Electrics-Eagles/Electric-Eagles/Documents/Safety/Drones and Battery  safety.pdf

Drones and Battery safety.

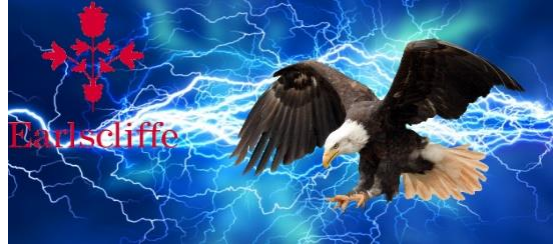
[picture p3: figure]

### 1 When somebody runs drone , everybody else wear

glasses ! And don`t go to drone near than 2 meters.

### 2 When command “Take off” is said everybody goes

away from drone to safe distance*.

### 3 When drone touches down nobody go near to

drone while command “Copter Disarmed” is said.

### 4 If you want change something in drone firstly

disconnect a battery.

### 5 When you flight with copter , do all movements

with sticks slowly.

### 6 Don`t leave battery in drone. Put it in safety

box**

### 7 Charge battery only using calibrated checked

charger . (During charging process don`t leave a room where it happened.

### 8 Think before do !

*- A metal isolated box .
** - Like IMAX B6 and others
