Electrics-Eagles/Electric-Eagles/Modules/EasyFly/Android APP/AndroidUSBCamera-master/gifs/download.png

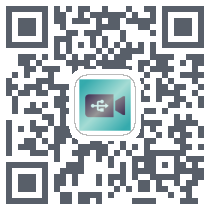
Modules/EasyFly/Android APP/AndroidUSBCamera-master/gifs/download.png
