Electrics-Eagles/Electric-Eagles/Tools Code/Died Tools/CopterChecktool/error.png

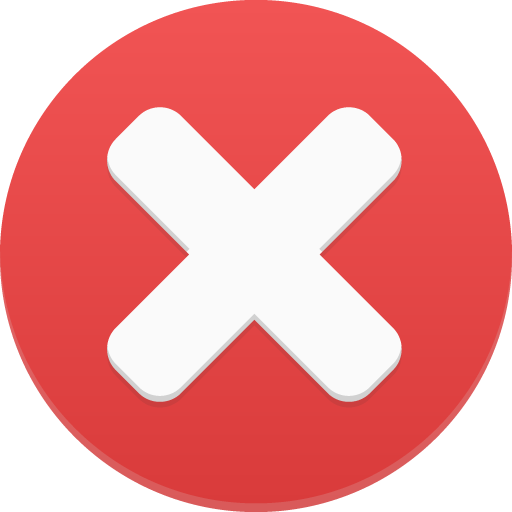
Tools Code/Died Tools/CopterChecktool/error.png
