Electrics-Eagles/Electric-Eagles/Tools Code/Died Tools/CopterChecktool/ok.png

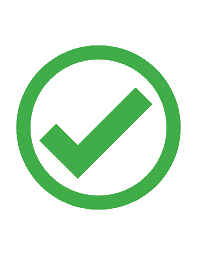
Tools Code/Died Tools/CopterChecktool/ok.png
