Electrics-Eagles/Electric-Eagles/Studio/Bugs/Build System. · Issue #3 · alex5250_ElectricsEaglesStudio.pdf

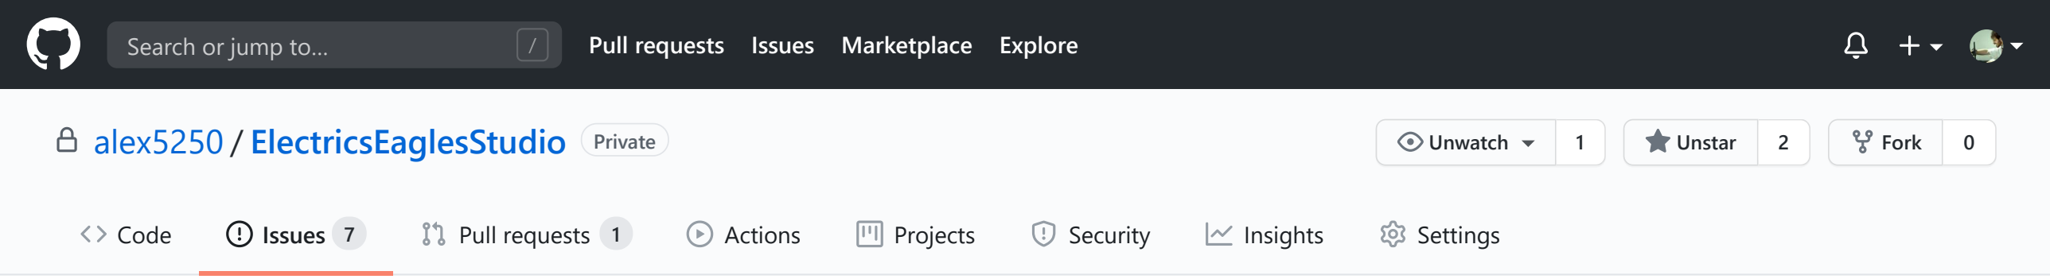
[picture p36: figure]
Code; Issues; Pull requests; Actions; Projects; Security; Insights; Settings; Search or jump to…; Pull requests Issues Marketplace Explore; Unwatch; Unstar; Fork

alex5250 (https://github.com/alex5250) / ElectricsEaglesStudio (https://github.com/alex5250/ElectricsEaglesStudio) Private

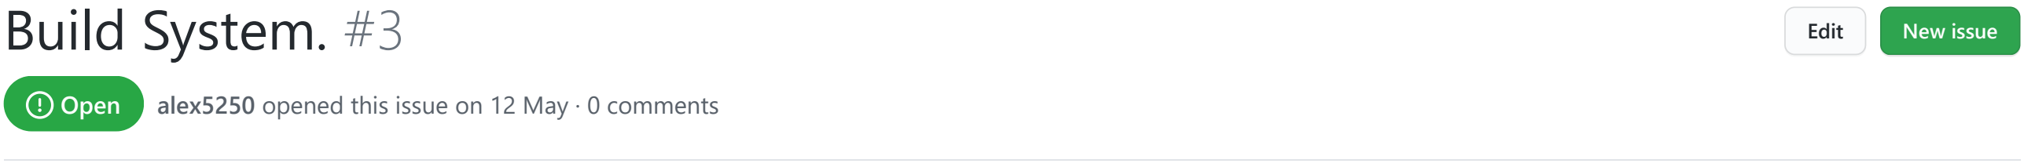
[picture p37: figure]
Build System. #3; Edit; New issue

Open alex5250 (https://github.com/alex5250) opened this issue on 12 May · 0 comments

No one—assign yourself

None yet

No milestone

Successfully merging a pull request may close this issue.
None yet

### 1 participant

Lock conversation

Pin issue

Transfer issue

Delete issue

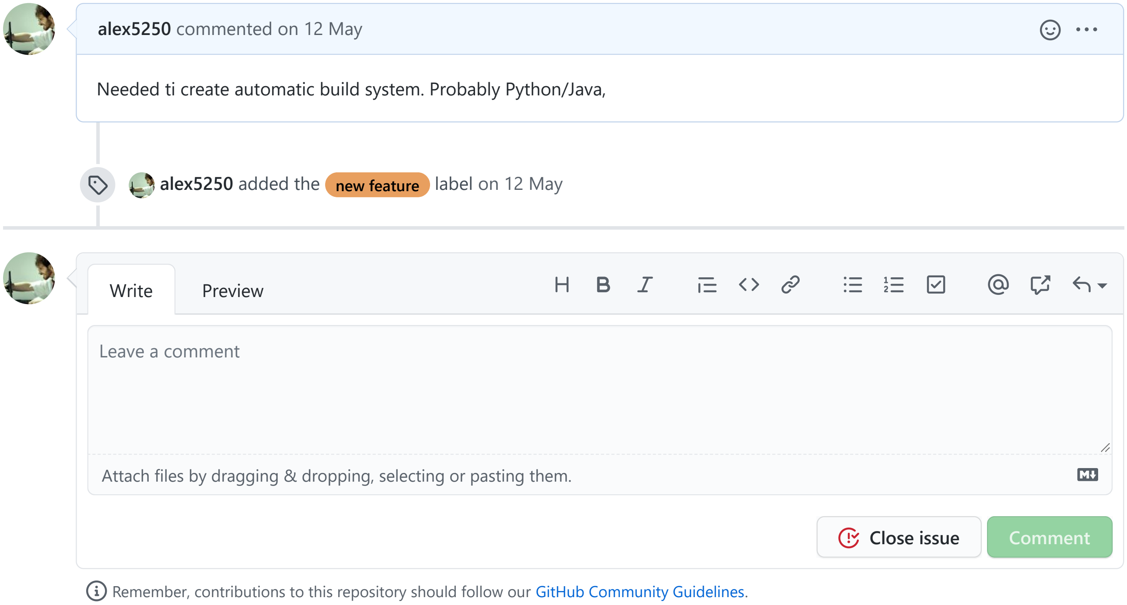
[picture p38: figure]
alex5250 commented on 12 May; alex5250 added the; new feature; label on 12 May; Leave a comment; Choose Files No file chosen; Close issue; Comment; Write; Preview

Needed ti create automatic build system. Probably Python/Java,

Remember, contributions to this repository should follow our GitHub Community Guidelines. (https://docs.github.com/articles/github-community-guidelines)

Attach files by dragging & dropping, selecting or pasting them.

Assignees

Labels

new feature (https://github.com/alex5250/ElectricsEaglesStudio/labels/new%20feature)

Projects

Milestone

Linked pull requests

You’re receiving notifications because you’re watching this repository.

Notifications | Customize

Unsubscribe

© 2020 GitHub, Inc. | Terms (https://github.com/site/terms) | Privacy (https://github.com/site/privacy) | Security (https://github.com/security) | Status (https://githubstatus.com/) | Help (https://docs.github.com/) | Contact GitHub (https://github.com/contact) | Pricing (https://github.com/pricing) | API (https://docs.github.com/) | Training (https://services.github.com/) | Blog (https://github.blog/) | About (https://github.com/about)
