Electrics-Eagles/Electric-Eagles/Studio/Electrics Eagles Setup Studio/src/main/resources/code.jpg

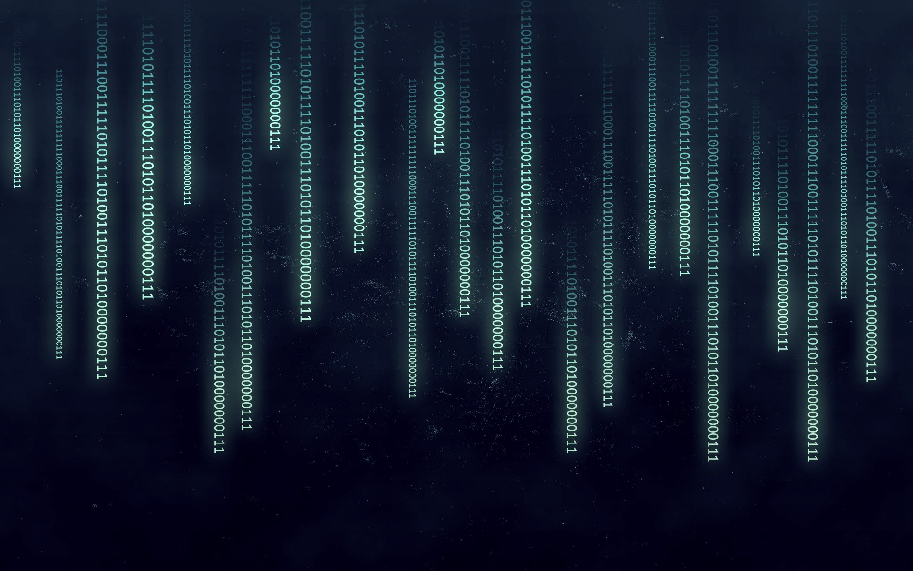
Studio/Electrics Eagles Setup Studio/src/main/resources/code.jpg
