Electrics-Eagles/Electric-Eagles/Studio/Electrics Eagles Setup Studio/src/main/resources/flash.png

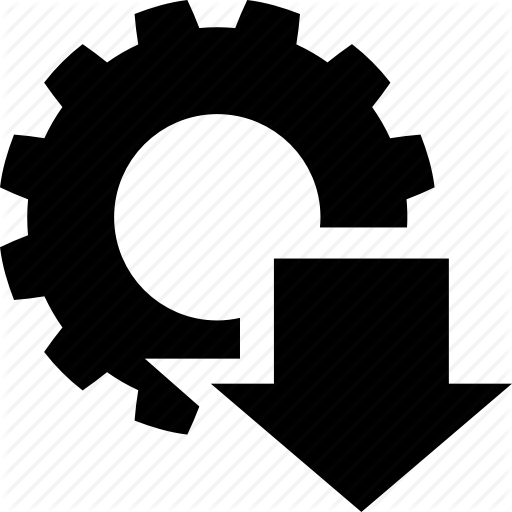
Studio/Electrics Eagles Setup Studio/src/main/resources/flash.png
