Electrics-Eagles/Electric-Eagles/Studio/Electrics Eagles Setup Studio/src/main/resources/Imanges/output_pd9a2z.gif

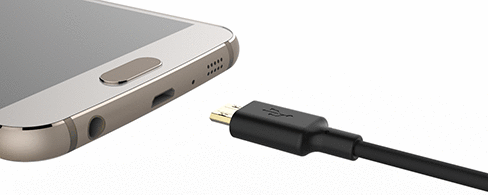
Studio/Electrics Eagles Setup Studio/src/main/resources/Imanges/output_pd9a2z.gif
