Electrics-Eagles/Electric-Eagles/Studio/Electrics Eagles Setup Studio/src/main/resources/Imanges/s7_usb_250px.gif

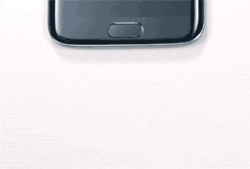
Studio/Electrics Eagles Setup Studio/src/main/resources/Imanges/s7_usb_250px.gif
