Electrics-Eagles/Electric-Eagles/Studio/Electrics Eagles Setup Studio/src/main/resources/pid.png

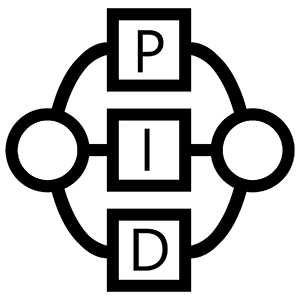
Studio/Electrics Eagles Setup Studio/src/main/resources/pid.png
