Electrics-Eagles/Electric-Eagles/Studio/Electrics Eagles Setup Studio/src/main/resources/usb-1831628-1554572.png

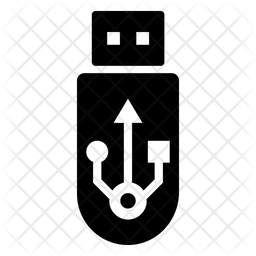
Studio/Electrics Eagles Setup Studio/src/main/resources/usb-1831628-1554572.png
