Electrics-Eagles/Electric-Eagles/Studio/Electrics Eagles Setup Studio/src/main/resources/VX2OTxL2oC.png

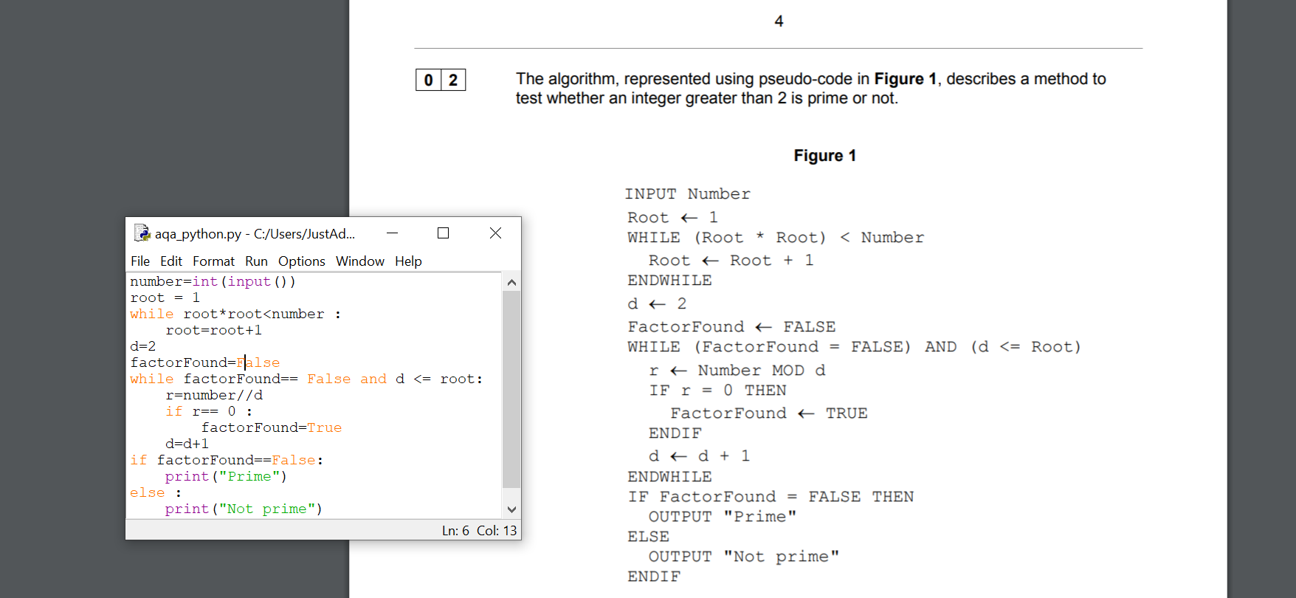
Studio/Electrics Eagles Setup Studio/src/main/resources/VX2OTxL2oC.png
