Electrics-Eagles/Electric-Eagles/Studio/Electrics Eagles Setup Studio/src/main/resources/x-512.png

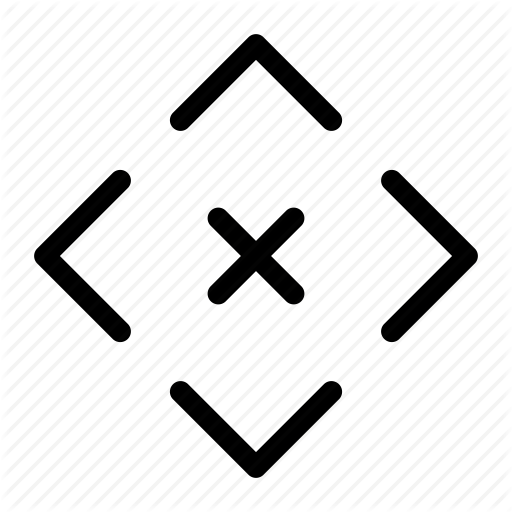
Studio/Electrics Eagles Setup Studio/src/main/resources/x-512.png
