Electrics-Eagles/Electric-Eagles/Studio/Bugs/PID Calibrate Button is not Working · Issue #12 · alex5250_ElectricsEaglesStudio.pdf

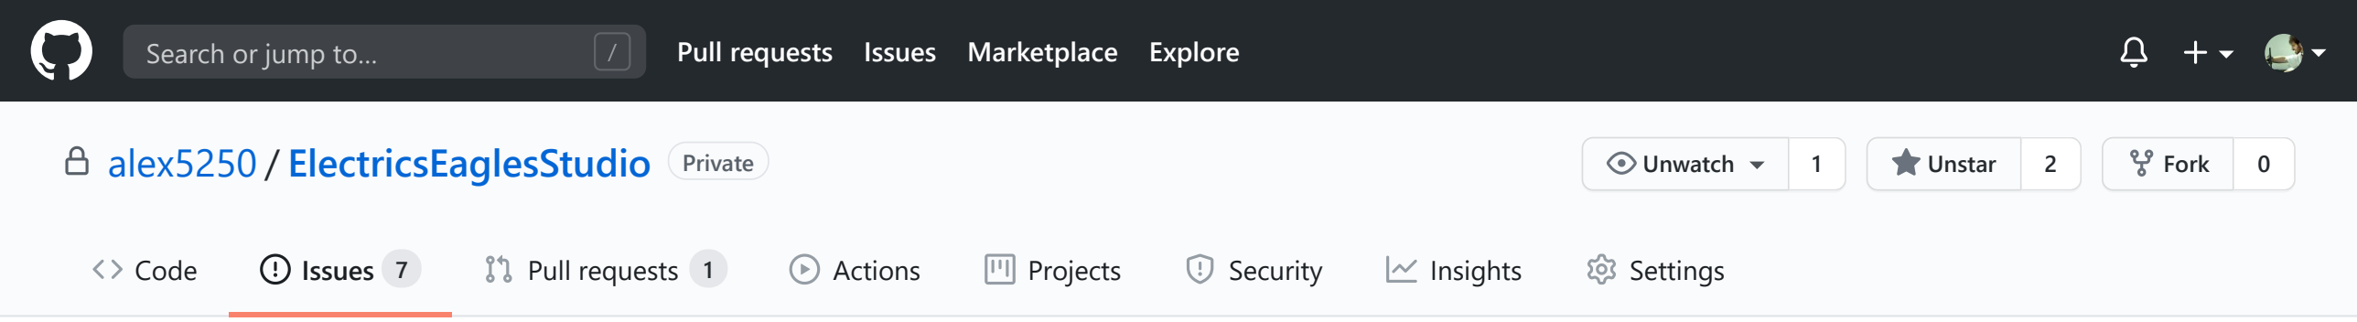
[picture p50: figure]
Unwatch; Unstar; Fork

alex5250 (https://github.com/alex5250) / ElectricsEaglesStudio (https://github.com/alex5250/ElectricsEaglesStudio) Private

Code (https://github.com/alex5250/ElectricsEaglesStudio) | Issues | 7 (https://github.com/alex5250/ElectricsEaglesStudio/issues) | Pull requests | 1 (https://github.com/alex5250/ElectricsEaglesStudio/pulls) | Actions (https://github.com/alex5250/ElectricsEaglesStudio/actions) | Projects (https://github.com/alex5250/ElectricsEaglesStudio/projects) | Security (https://github.com/alex5250/ElectricsEaglesStudio/security) | Insights (https://github.com/alex5250/ElectricsEaglesStudio/network/dependencies) | Settings (https://github.com/alex5250/ElectricsEaglesStudio/settings)

# PID Calibrate Button is not Working #12

## Open alex5250 (https://github.com/alex5250) opened this issue on 15 May · 0 comments

No one—assign yourself

None yet

No milestone

Successfully merging a pull request may close this issue.
None yet

### 1 participant

Lock conversation

Pin issue

Transfer issue

Delete issue

Search or jump to… | Pull requests (https://github.com/pulls) Issues (https://github.com/issues) Marketplace (https://github.com/marketplace) Explore (https://github.com/explore)
Edit | New issue (https://github.com/alex5250/ElectricsEaglesStudio/issues/new/choose)

## alex5250 (https://github.com/alex5250) commented on 15 May •

## 1. I opened a studio 2. Clicked an Open PID/Setup settings 3.Enter values

3. Press save values.

## 4. Pressed flash drone

5. I had an error.

## log.txt (https://github.com/alex5250/ElectricsEaglesStudio/files/4636048/log.txt)

system_info.txt (https://github.com/alex5250/ElectricsEaglesStudio/files/4636028/system_info.txt)

I got bug.

[INFO] Fri May 15 17:56:49 BST 2020 Found boards[Ljava.lang.String;@742f7e36 EXPORT TO : log.txt
[INFO] Fri May 15 17:56:52 BST 2020 Python is found EXPORT TO : log.txt
[ERROR] Fri May 15 17:56:52 BST 2020 Python is found EXPORT TO : log.txt
[INFO] Fri May 15 17:56:52 BST 2020 Load an scene ./src/main/resources/main_window.fxml style type: DECORATED EXPOR 0.0
525.0
494.0
It is a small module
[INFO] Fri May 15 17:56:57 BST 2020 Open an gui EXPORT TO : log.txt
MLANG CONFIG INTEPETER VERISON: 1.0.243532
C:\Users\Alex\Documents\image\bin\src\main\resources\Wirzard.FXML
[INFO] Fri May 15 17:57:29 BST 2020 Load an scene C:\Users\Alex\Documents\image\bin\src\main\resources\Wirzard.FXML [INFO] Fri May 15 17:57:29 BST 2020 Open an gui EXPORT TO : log.txt
[INFO] Fri May 15 17:57:29 BST 2020 Run an app.Wirzard Step 2 EXPORT TO : log.txt
[INFO] Fri May 15 17:57:31 BST 2020 Load an scene ./src/main/resources/PID_KALMAN/pid_settings.fxml style type: UTI [INFO] Fri May 15 17:57:31 BST 2020 Open an gui EXPORT TO : log.txt
[INFO] Fri May 15 17:57:31 BST 2020 Run an P.I.D Setting EXPORT TO : log.txt C:\Users\Alex\Documents\image\bin\src\main\resources\app.Wirzard.FXML
Exception in thread "JavaFX Application Thread" java.lang.RuntimeException: java.lang.reflect.InvocationTargetExcept at javafx.fxml/javafx.fxml.FXMLLoader$MethodHandler.invoke(Unknown Source)
at javafx.fxml/javafx.fxml.FXMLLoader$ControllerMethodEventHandler.handle(Unknown Source)
at javafx.base/com.sun.javafx.event.CompositeEventHandler.dispatchBubblingEvent(Unknown Source) at javafx.base/com.sun.javafx.event.EventHandlerManager.dispatchBubblingEvent(Unknown Source)
at javafx.base/com.sun.javafx.event.EventHandlerManager.dispatchBubblingEvent(Unknown Source)
at javafx.base/com.sun.javafx.event.CompositeEventDispatcher.dispatchBubblingEvent(Unknown Source) at javafx.base/com.sun.javafx.event.BasicEventDispatcher.dispatchEvent(Unknown Source)
at javafx.base/com.sun.javafx.event.EventDispatchChainImpl.dispatchEvent(Unknown Source)
at javafx.base/com.sun.javafx.event.BasicEventDispatcher.dispatchEvent(Unknown Source)
at javafx.base/com.sun.javafx.event.EventDispatchChainImpl.dispatchEvent(Unknown Source) at javafx.base/com.sun.javafx.event.BasicEventDispatcher.dispatchEvent(Unknown Source) at javafx.base/com.sun.javafx.event.EventDispatchChainImpl.dispatchEvent(Unknown Source) at javafx.base/com.sun.javafx.event.EventUtil.fireEventImpl(Unknown Source)
at javafx.base/com.sun.javafx.event.EventUtil.fireEvent(Unknown Source)
at javafx.base/javafx.event.Event.fireEvent(Unknown Source)
at javafx.graphics/javafx.scene.Scene$ClickGenerator.postProcess(Unknown Source) at javafx.graphics/javafx.scene.Scene$MouseHandler.process(Unknown Source)
at javafx.graphics/javafx.scene.Scene.processMouseEvent(Unknown Source)
at javafx.graphics/javafx.scene.Scene$ScenePeerListener.mouseEvent(Unknown Source)
at javafx.graphics/com.sun.javafx.tk.quantum.GlassViewEventHandler$MouseEventNotification.run(Unknown Source at javafx.graphics/com.sun.javafx.tk.quantum.GlassViewEventHandler$MouseEventNotification.run(Unknown Source at java.base/java.security.AccessController.doPrivileged(Native Method)
at javafx.graphics/com.sun.javafx.tk.quantum.GlassViewEventHandler.lambda$handleMouseEvent$2(Unknown Source) at javafx.graphics/com.sun.javafx.tk.quantum.QuantumToolkit.runWithoutRenderLock(Unknown Source)
at javafx.graphics/com.sun.javafx.tk.quantum.GlassViewEventHandler.handleMouseEvent(Unknown Source)
at javafx.graphics/com.sun.glass.ui.View.handleMouseEvent(Unknown Source)
at javafx.graphics/com.sun.glass.ui.View.notifyMouse(Unknown Source)
at javafx.graphics/com.sun.glass.ui.win.WinApplication._runLoop(Native Method)
at javafx.graphics/com.sun.glass.ui.win.WinApplication.lambda$runLoop$3(Unknown Source) at java.base/java.lang.Thread.run(Unknown Source)
Caused by: java.lang.reflect.InvocationTargetException at java.base/jdk.internal.reflect.NativeMethodAccessorImpl.invoke0(Native Method)
at java.base/jdk.internal.reflect.NativeMethodAccessorImpl.invoke(Unknown Source) at java.base/jdk.internal.reflect.DelegatingMethodAccessorImpl.invoke(Unknown Source) at java.base/java.lang.reflect.Method.invoke(Unknown Source)
at com.sun.javafx.reflect.Trampoline.invoke(Unknown Source)
at jdk.internal.reflect.GeneratedMethodAccessor2.invoke(Unknown Source)
at java.base/jdk.internal.reflect.DelegatingMethodAccessorImpl.invoke(Unknown Source) at java.base/java.lang.reflect.Method.invoke(Unknown Source)
at javafx.base/com.sun.javafx.reflect.MethodUtil.invoke(Unknown Source)
at javafx.fxml/com.sun.javafx.fxml.MethodHelper.invoke(Unknown Source)
... 30 more
Caused by: java.lang.NullPointerException at Electrics.Eagles.Setup.Studio.main/app.PID_Setup.Controller.reflash(Unknown Source) ... 40 more

## edited

alex5250 (https://github.com/alex5250) added the | bug (https://github.com/alex5250/ElectricsEaglesStudio/labels/bug) | label on 15 May

Remember, contributions to this repository should follow our GitHub Community Guidelines. (https://docs.github.com/articles/github-community-guidelines)

## Leave a comment

Attach files by dragging & dropping, selecting or pasting them.

## Choose Files No file chosen

## Close issue Comment

Assignees

Labels

bug (https://github.com/alex5250/ElectricsEaglesStudio/labels/bug)

Projects

Milestone

Linked pull requests

You’re receiving notifications because you’re watching this repository.

Notifications | Customize

Unsubscribe

© 2020 GitHub, Inc. | Terms (https://github.com/site/terms) | Privacy (https://github.com/site/privacy) | Security (https://github.com/security) | Status (https://githubstatus.com/) | Help (https://docs.github.com/) | Contact GitHub (https://github.com/contact) | Pricing (https://github.com/pricing) | API (https://docs.github.com/) | Training (https://services.github.com/) | Blog (https://github.blog/) | About (https://github.com/about)
Write | Preview
