Electrics-Eagles/Electric-Eagles/Studio/Electrics Eagles Setup Studio/src/main/resources/Wirzard.FXML/Calibrate/fail.jpg

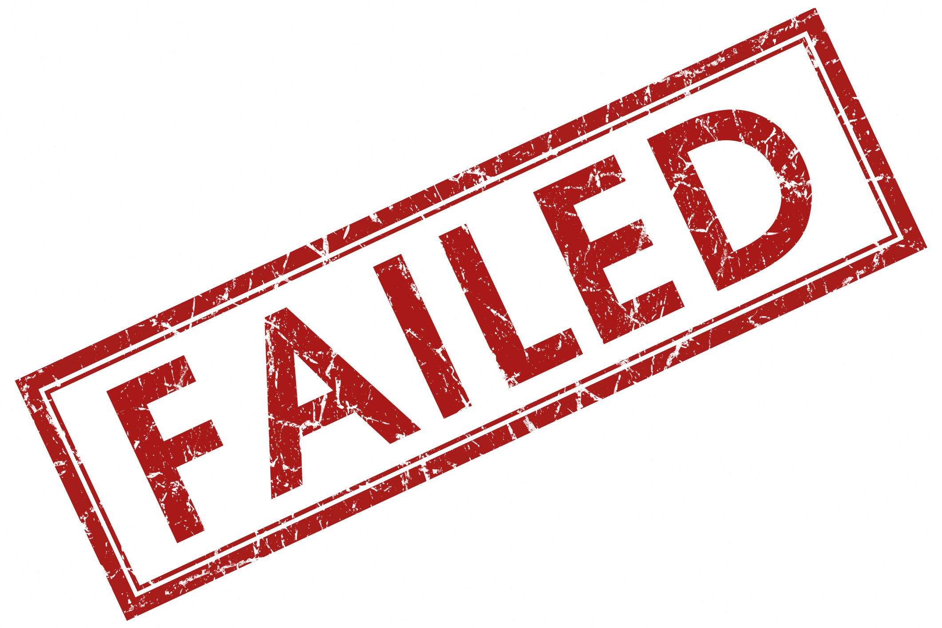
Studio/Electrics Eagles Setup Studio/src/main/resources/Wirzard.FXML/Calibrate/fail.jpg
