Electrics-Eagles/Electric-Eagles/Tools Code/Died Tools/CopterSetUpTool/src/Main_GUI.py

# -*- coding: utf-8 -*-

# Form implementation generated from reading ui file 'C:\Users\DroneDeveloper\PycharmProjects\CopterSetUpTool\Main_GUI.ui'
#
# Created by: PyQt5 UI code generator 5.13.0
#
# WARNING! All changes made in this file will be lost!


from PyQt5 import QtCore, QtGui, QtWidgets


class Ui_MainWindow(object):
    def setupUi(self, MainWindow):
        MainWindow.setObjectName("MainWindow")
        MainWindow.resize(800, 600)
        MainWindow.setStyleSheet("/* ---------------------------------------------------------------------------\n"
"\n"
"    Created by the qtsass compiler\n"
"\n"
"    WARNING! All changes made in this file will be lost!\n"
"\n"
"--------------------------------------------------------------------------- */\n"
"/* QDarkStyleSheet -----------------------------------------------------------\n"
"\n"
"This is the main style sheet, the palette has eight colors.\n"
"\n"
"It is based on three selecting colors, three greyish (background) colors\n"
"plus three whitish (foreground) colors. Each set of widgets of the same\n"
"type have a header like this:\n"
"\n"
"    ------------------\n"
"    GroupName --------\n"
"    ------------------\n"
"\n"
"And each widget is separated with a header like this:\n"
"\n"
"    QWidgetName ------\n"
"\n"
"This makes more easy to find and change some css field. The basic\n"
"configuration is described bellow.\n"
"\n"
"    BACKGROUND -----------\n"
"\n"
"        Light  #4D545B #505F69 (unpressed)\n"
"        Normal #31363B #32414B (border, disabled, pressed, checked, toolbars, menus)\n"
"        Dark   #232629 #19232D (background)\n"
"\n"
"    FOREGROUND -----------\n"
"\n"
"        Light  #EFF0F1 #F0F0F0 (texts/labels)\n"
"        Normal         #AAAAAA (not used yet)\n"
"        Dark   #505F69 #787878 (disabled texts)\n"
"\n"
"    SELECTION ------------\n"
"\n"
"        Light  #179AE0 #148CD2 (selection/hover/active)\n"
"        Normal #3375A3 #1464A0 (selected)\n"
"        Dark   #18465D #14506E (selected disabled)\n"
"\n"
"If a stranger configuration is required because of a bugfix or anything\n"
"else, keep the comment on the line above so nobody changes it, including the\n"
"issue number.\n"
"\n"
"*/\n"
"/*\n"
"\n"
"See Qt documentation:\n"
"\n"
"  - https://doc.qt.io/qt-5/stylesheet.html\n"
"  - https://doc.qt.io/qt-5/stylesheet-reference.html\n"
"  - https://doc.qt.io/qt-5/stylesheet-examples.html\n"
"\n"
"--------------------------------------------------------------------------- */\n"
"/* QWidget ----------------------------------------------------------------\n"
"\n"
"--------------------------------------------------------------------------- */\n"
"QWidget {\n"
"  background-color: #19232D;\n"
"  border: 0px solid #32414B;\n"
"  padding: 0px;\n"
"  color: #F0F0F0;\n"
"  selection-background-color: #1464A0;\n"
"  selection-color: #F0F0F0;\n"
"}\n"
"\n"
"QWidget:disabled {\n"
"  background-color: #19232D;\n"
"  color: #787878;\n"
"  selection-background-color: #14506E;\n"
"  selection-color: #787878;\n"
"}\n"
"\n"
"QWidget::item:selected {\n"
"  background-color: #1464A0;\n"
"}\n"
"\n"
"QWidget::item:hover {\n"
"  background-color: #148CD2;\n"
"  color: #32414B;\n"
"}\n"
"\n"
"/* QMainWindow ------------------------------------------------------------\n"
"\n"
"This adjusts the splitter in the dock widget, not qsplitter\n"
"\n"
"https://doc.qt.io/qt-5/stylesheet-examples.html#customizing-qmainwindow\n"
"\n"
"--------------------------------------------------------------------------- */\n"
"QMainWindow::separator {\n"
"  background-color: #32414B;\n"
"  border: 0px solid #19232D;\n"
"  spacing: 0px;\n"
"  padding: 2px;\n"
"}\n"
"\n"
"QMainWindow::separator:hover {\n"
"  background-color: #505F69;\n"
"  border: 0px solid #148CD2;\n"
"}\n"
"\n"
"QMainWindow::separator:horizontal {\n"
"  width: 5px;\n"
"  margin-top: 2px;\n"
"  margin-bottom: 2px;\n"
"  image: url(\":/qss_icons/rc/toolbar_separator_vertical.png\");\n"
"}\n"
"\n"
"QMainWindow::separator:vertical {\n"
"  height: 5px;\n"
"  margin-left: 2px;\n"
"  margin-right: 2px;\n"
"  image: url(\":/qss_icons/rc/toolbar_separator_horizontal.png\");\n"
"}\n"
"\n"
"/* QToolTip ---------------------------------------------------------------\n"
"\n"
"https://doc.qt.io/qt-5/stylesheet-examples.html#customizing-qtooltip\n"
"\n"
"--------------------------------------------------------------------------- */\n"
"QToolTip {\n"
"  background-color: #148CD2;\n"
"  border: 1px solid #19232D;\n"
"  color: #19232D;\n"
"  /* Remove padding, for fix combo box tooltip */\n"
"  padding: 0px;\n"
"  /* Reducing transparency to read better */\n"
"  opacity: 230;\n"
"}\n"
"\n"
"/* QStatusBar -------------------------------------------------------------\n"
"\n"
"https://doc.qt.io/qt-5/stylesheet-examples.html#customizing-qstatusbar\n"
"\n"
"--------------------------------------------------------------------------- */\n"
"QStatusBar {\n"
"  border: 1px solid #32414B;\n"
"  /* Fixes Spyder #9120, #9121 */\n"
"  background: #32414B;\n"
"}\n"
"\n"
"QStatusBar QToolTip {\n"
"  background-color: #148CD2;\n"
"  border: 1px solid #19232D;\n"
"  color: #19232D;\n"
"  /* Remove padding, for fix combo box tooltip */\n"
"  padding: 0px;\n"
"  /* Reducing transparency to read better */\n"
"  opacity: 230;\n"
"}\n"
"\n"
"QStatusBar QLabel {\n"
"  /* Fixes Spyder #9120, #9121 */\n"
"  background: transparent;\n"
"}\n"
"\n"
"/* QCheckBox --------------------------------------------------------------\n"
"\n"
"https://doc.qt.io/qt-5/stylesheet-examples.html#customizing-qcheckbox\n"
"\n"
"--------------------------------------------------------------------------- */\n"
"QCheckBox {\n"
"  background-color: #19232D;\n"
"  color: #F0F0F0;\n"
"  spacing: 4px;\n"
"  outline: none;\n"
"  padding-top: 4px;\n"
"  padding-bottom: 4px;\n"
"}\n"
"\n"
"QCheckBox:focus {\n"
"  border: none;\n"
"}\n"
"\n"
"QCheckBox QWidget:disabled {\n"
"  background-color: #19232D;\n"
"  color: #787878;\n"
"}\n"
"\n"
"QCheckBox::indicator {\n"
"  margin-left: 4px;\n"
"  height: 16px;\n"
"  width: 16px;\n"
"}\n"
"\n"
"QCheckBox::indicator:unchecked {\n"
"  image: url(\":/qss_icons/rc/checkbox_unchecked.png\");\n"
"}\n"
"\n"
"QCheckBox::indicator:unchecked:hover, QCheckBox::indicator:unchecked:focus, QCheckBox::indicator:unchecked:pressed {\n"
"  border: none;\n"
"  image: url(\":/qss_icons/rc/checkbox_unchecked_focus.png\");\n"
"}\n"
"\n"
"QCheckBox::indicator:unchecked:disabled {\n"
"  image: url(\":/qss_icons/rc/checkbox_unchecked_disabled.png\");\n"
"}\n"
"\n"
"QCheckBox::indicator:checked {\n"
"  image: url(\":/qss_icons/rc/checkbox_checked.png\");\n"
"}\n"
"\n"
"QCheckBox::indicator:checked:hover, QCheckBox::indicator:checked:focus, QCheckBox::indicator:checked:pressed {\n"
"  border: none;\n"
"  image: url(\":/qss_icons/rc/checkbox_checked_focus.png\");\n"
"}\n"
"\n"
"QCheckBox::indicator:checked:disabled {\n"
"  image: url(\":/qss_icons/rc/checkbox_checked_disabled.png\");\n"
"}\n"
"\n"
"QCheckBox::indicator:indeterminate {\n"
"  image: url(\":/qss_icons/rc/checkbox_indeterminate.png\");\n"
"}\n"
"\n"
"QCheckBox::indicator:indeterminate:disabled {\n"
"  image: url(\":/qss_icons/rc/checkbox_indeterminate_disabled.png\");\n"
"}\n"
"\n"
"QCheckBox::indicator:indeterminate:focus, QCheckBox::indicator:indeterminate:hover, QCheckBox::indicator:indeterminate:pressed {\n"
"  image: url(\":/qss_icons/rc/checkbox_indeterminate_focus.png\");\n"
"}\n"
"\n"
"/* QGroupBox --------------------------------------------------------------\n"
"\n"
"https://doc.qt.io/qt-5/stylesheet-examples.html#customizing-qgroupbox\n"
"\n"
"--------------------------------------------------------------------------- */\n"
"QGroupBox {\n"
"  font-weight: bold;\n"
"  border: 1px solid #32414B;\n"
"  border-radius: 4px;\n"
"  padding: 4px;\n"
"  margin-top: 16px;\n"
"}\n"
"\n"
"QGroupBox::title {\n"
"  subcontrol-origin: margin;\n"
"  subcontrol-position: top left;\n"
"  left: 3px;\n"
"  padding-left: 3px;\n"
"  padding-right: 5px;\n"
"  padding-top: 8px;\n"
"  padding-bottom: 16px;\n"
"}\n"
"\n"
"QGroupBox::indicator {\n"
"  margin-left: 2px;\n"
"  height: 12px;\n"
"  width: 12px;\n"
"}\n"
"\n"
"QGroupBox::indicator:unchecked:hover, QGroupBox::indicator:unchecked:focus, QGroupBox::indicator:unchecked:pressed {\n"
"  border: none;\n"
"  image: url(\":/qss_icons/rc/checkbox_unchecked_focus.png\");\n"
"}\n"
"\n"
"QGroupBox::indicator:unchecked:disabled {\n"
"  image: url(\":/qss_icons/rc/checkbox_unchecked_disabled.png\");\n"
"}\n"
"\n"
"QGroupBox::indicator:checked:hover, QGroupBox::indicator:checked:focus, QGroupBox::indicator:checked:pressed {\n"
"  border: none;\n"
"  image: url(\":/qss_icons/rc/checkbox_checked_focus.png\");\n"
"}\n"
"\n"
"QGroupBox::indicator:checked:disabled {\n"
"  image: url(\":/qss_icons/rc/checkbox_checked_disabled.png\");\n"
"}\n"
"\n"
"/* QRadioButton -----------------------------------------------------------\n"
"\n"
"https://doc.qt.io/qt-5/stylesheet-examples.html#customizing-qradiobutton\n"
"\n"
"--------------------------------------------------------------------------- */\n"
"QRadioButton {\n"
"  background-color: #19232D;\n"
"  color: #F0F0F0;\n"
"  spacing: 4px;\n"
"  padding: 0px;\n"
"  border: none;\n"
"  outline: none;\n"
"}\n"
"\n"
"QRadioButton:focus {\n"
"  border: none;\n"
"}\n"
"\n"
"QRadioButton:disabled {\n"
"  background-color: #19232D;\n"
"  color: #787878;\n"
"  border: none;\n"
"  outline: none;\n"
"}\n"
"\n"
"QRadioButton QWidget {\n"
"  background-color: #19232D;\n"
"  color: #F0F0F0;\n"
"  spacing: 0px;\n"
"  padding: 0px;\n"
"  outline: none;\n"
"  border: none;\n"
"}\n"
"\n"
"QRadioButton::indicator {\n"
"  border: none;\n"
"  outline: none;\n"
"  margin-left: 4px;\n"
"  height: 16px;\n"
"  width: 16px;\n"
"}\n"
"\n"
"QRadioButton::indicator:unchecked {\n"
"  image: url(\":/qss_icons/rc/radio_unchecked.png\");\n"
"}\n"
"\n"
"QRadioButton::indicator:unchecked:hover, QRadioButton::indicator:unchecked:focus, QRadioButton::indicator:unchecked:pressed {\n"
"  border: none;\n"
"  outline: none;\n"
"  image: url(\":/qss_icons/rc/radio_unchecked_focus.png\");\n"
"}\n"
"\n"
"QRadioButton::indicator:unchecked:disabled {\n"
"  image: url(\":/qss_icons/rc/radio_unchecked_disabled.png\");\n"
"}\n"
"\n"
"QRadioButton::indicator:checked {\n"
"  border: none;\n"
"  outline: none;\n"
"  image: url(\":/qss_icons/rc/radio_checked.png\");\n"
"}\n"
"\n"
"QRadioButton::indicator:checked:hover, QRadioButton::indicator:checked:focus, QRadioButton::indicator:checked:pressed {\n"
"  border: none;\n"
"  outline: none;\n"
"  image: url(\":/qss_icons/rc/radio_checked_focus.png\");\n"
"}\n"
"\n"
"QRadioButton::indicator:checked:disabled {\n"
"  outline: none;\n"
"  image: url(\":/qss_icons/rc/radio_checked_disabled.png\");\n"
"}\n"
"\n"
"/* QMenuBar ---------------------------------------------------------------\n"
"\n"
"https://doc.qt.io/qt-5/stylesheet-examples.html#customizing-qmenubar\n"
"\n"
"--------------------------------------------------------------------------- */\n"
"QMenuBar {\n"
"  background-color: #32414B;\n"
"  padding: 2px;\n"
"  border: 1px solid #19232D;\n"
"  color: #F0F0F0;\n"
"}\n"
"\n"
"QMenuBar:focus {\n"
"  border: 1px solid #148CD2;\n"
"}\n"
"\n"
"QMenuBar::item {\n"
"  background: transparent;\n"
"  padding: 4px;\n"
"}\n"
"\n"
"QMenuBar::item:selected {\n"
"  padding: 4px;\n"
"  background: transparent;\n"
"  border: 0px solid #32414B;\n"
"}\n"
"\n"
"QMenuBar::item:pressed {\n"
"  padding: 4px;\n"
"  border: 0px solid #32414B;\n"
"  background-color: #148CD2;\n"
"  color: #F0F0F0;\n"
"  margin-bottom: 0px;\n"
"  padding-bottom: 0px;\n"
"}\n"
"\n"
"/* QMenu ------------------------------------------------------------------\n"
"\n"
"https://doc.qt.io/qt-5/stylesheet-examples.html#customizing-qmenu\n"
"\n"
"--------------------------------------------------------------------------- */\n"
"QMenu {\n"
"  border: 0px solid #32414B;\n"
"  color: #F0F0F0;\n"
"  margin: 0px;\n"
"}\n"
"\n"
"QMenu::separator {\n"
"  height: 1px;\n"
"  background-color: #505F69;\n"
"  color: #F0F0F0;\n"
"}\n"
"\n"
"QMenu::icon {\n"
"  margin: 0px;\n"
"  padding-left: 4px;\n"
"}\n"
"\n"
"QMenu::item {\n"
"  background-color: #32414B;\n"
"  padding: 4px 24px 4px 24px;\n"
"  /* Reserve space for selection border */\n"
"  border: 1px transparent #32414B;\n"
"}\n"
"\n"
"QMenu::item:selected {\n"
"  color: #F0F0F0;\n"
"}\n"
"\n"
"QMenu::indicator {\n"
"  width: 12px;\n"
"  height: 12px;\n"
"  padding-left: 6px;\n"
"  /* non-exclusive indicator = check box style indicator (see QActionGroup::setExclusive) */\n"
"  /* exclusive indicator = radio button style indicator (see QActionGroup::setExclusive) */\n"
"}\n"
"\n"
"QMenu::indicator:non-exclusive:unchecked {\n"
"  image: url(\":/qss_icons/rc/checkbox_unchecked.png\");\n"
"}\n"
"\n"
"QMenu::indicator:non-exclusive:unchecked:selected {\n"
"  image: url(\":/qss_icons/rc/checkbox_unchecked_disabled.png\");\n"
"}\n"
"\n"
"QMenu::indicator:non-exclusive:checked {\n"
"  image: url(\":/qss_icons/rc/checkbox_checked.png\");\n"
"}\n"
"\n"
"QMenu::indicator:non-exclusive:checked:selected {\n"
"  image: url(\":/qss_icons/rc/checkbox_checked_disabled.png\");\n"
"}\n"
"\n"
"QMenu::indicator:exclusive:unchecked {\n"
"  image: url(\":/qss_icons/rc/radio_unchecked.png\");\n"
"}\n"
"\n"
"QMenu::indicator:exclusive:unchecked:selected {\n"
"  image: url(\":/qss_icons/rc/radio_unchecked_disabled.png\");\n"
"}\n"
"\n"
"QMenu::indicator:exclusive:checked {\n"
"  image: url(\":/qss_icons/rc/radio_checked.png\");\n"
"}\n"
"\n"
"QMenu::indicator:exclusive:checked:selected {\n"
"  image: url(\":/qss_icons/rc/radio_checked_disabled.png\");\n"
"}\n"
"\n"
"QMenu::right-arrow {\n"
"  margin: 5px;\n"
"  image: url(\":/qss_icons/rc/arrow_right.png\");\n"
"  height: 12px;\n"
"  width: 12px;\n"
"}\n"
"\n"
"/* QAbstractItemView ------------------------------------------------------\n"
"\n"
"https://doc.qt.io/qt-5/stylesheet-examples.html#customizing-qcombobox\n"
"\n"
"--------------------------------------------------------------------------- */\n"
"QAbstractItemView {\n"
"  alternate-background-color: #19232D;\n"
"  color: #F0F0F0;\n"
"  border: 1px solid #32414B;\n"
"  border-radius: 4px;\n"
"}\n"
"\n"
"QAbstractItemView QLineEdit {\n"
"  padding: 2px;\n"
"}\n"
"\n"
"/* QAbstractScrollArea ----------------------------------------------------\n"
"\n"
"https://doc.qt.io/qt-5/stylesheet-examples.html#customizing-qabstractscrollarea\n"
"\n"
"--------------------------------------------------------------------------- */\n"
"QAbstractScrollArea {\n"
"  background-color: #19232D;\n"
"  border: 1px solid #32414B;\n"
"  border-radius: 4px;\n"
"  padding: 2px;\n"
"  /* fix #159 */\n"
"  min-height: 1.25em;\n"
"  /* fix #159 */\n"
"  color: #F0F0F0;\n"
"}\n"
"\n"
"QAbstractScrollArea:disabled {\n"
"  color: #787878;\n"
"}\n"
"\n"
"/* QScrollArea ------------------------------------------------------------\n"
"\n"
"--------------------------------------------------------------------------- */\n"
"QScrollArea QWidget QWidget:disabled {\n"
"  background-color: #19232D;\n"
"}\n"
"\n"
"/* QScrollBar -------------------------------------------------------------\n"
"\n"
"https://doc.qt.io/qt-5/stylesheet-examples.html#customizing-qscrollbar\n"
"\n"
"--------------------------------------------------------------------------- */\n"
"QScrollBar:horizontal {\n"
"  height: 16px;\n"
"  margin: 2px 16px 2px 16px;\n"
"  border: 1px solid #32414B;\n"
"  border-radius: 4px;\n"
"  background-color: #19232D;\n"
"}\n"
"\n"
"QScrollBar:vertical {\n"
"  background-color: #19232D;\n"
"  width: 16px;\n"
"  margin: 16px 2px 16px 2px;\n"
"  border: 1px solid #32414B;\n"
"  border-radius: 4px;\n"
"}\n"
"\n"
"QScrollBar::handle:horizontal {\n"
"  background-color: #787878;\n"
"  border: 1px solid #32414B;\n"
"  border-radius: 4px;\n"
"  min-width: 8px;\n"
"}\n"
"\n"
"QScrollBar::handle:horizontal:hover {\n"
"  background-color: #148CD2;\n"
"  border: 1px solid #148CD2;\n"
"  border-radius: 4px;\n"
"  min-width: 8px;\n"
"}\n"
"\n"
"QScrollBar::handle:vertical {\n"
"  background-color: #787878;\n"
"  border: 1px solid #32414B;\n"
"  min-height: 8px;\n"
"  border-radius: 4px;\n"
"}\n"
"\n"
"QScrollBar::handle:vertical:hover {\n"
"  background-color: #148CD2;\n"
"  border: 1px solid #148CD2;\n"
"  border-radius: 4px;\n"
"  min-height: 8px;\n"
"}\n"
"\n"
"QScrollBar::add-line:horizontal {\n"
"  margin: 0px 0px 0px 0px;\n"
"  border-image: url(\":/qss_icons/rc/arrow_right_disabled.png\");\n"
"  height: 12px;\n"
"  width: 12px;\n"
"  subcontrol-position: right;\n"
"  subcontrol-origin: margin;\n"
"}\n"
"\n"
"QScrollBar::add-line:horizontal:hover, QScrollBar::add-line:horizontal:on {\n"
"  border-image: url(\":/qss_icons/rc/arrow_right.png\");\n"
"  height: 12px;\n"
"  width: 12px;\n"
"  subcontrol-position: right;\n"
"  subcontrol-origin: margin;\n"
"}\n"
"\n"
"QScrollBar::add-line:vertical {\n"
"  margin: 3px 0px 3px 0px;\n"
"  border-image: url(\":/qss_icons/rc/arrow_down_disabled.png\");\n"
"  height: 12px;\n"
"  width: 12px;\n"
"  subcontrol-position: bottom;\n"
"  subcontrol-origin: margin;\n"
"}\n"
"\n"
"QScrollBar::add-line:vertical:hover, QScrollBar::add-line:vertical:on {\n"
"  border-image: url(\":/qss_icons/rc/arrow_down.png\");\n"
"  height: 12px;\n"
"  width: 12px;\n"
"  subcontrol-position: bottom;\n"
"  subcontrol-origin: margin;\n"
"}\n"
"\n"
"QScrollBar::sub-line:horizontal {\n"
"  margin: 0px 3px 0px 3px;\n"
"  border-image: url(\":/qss_icons/rc/arrow_left_disabled.png\");\n"
"  height: 12px;\n"
"  width: 12px;\n"
"  subcontrol-position: left;\n"
"  subcontrol-origin: margin;\n"
"}\n"
"\n"
"QScrollBar::sub-line:horizontal:hover, QScrollBar::sub-line:horizontal:on {\n"
"  border-image: url(\":/qss_icons/rc/arrow_left.png\");\n"
"  height: 12px;\n"
"  width: 12px;\n"
"  subcontrol-position: left;\n"
"  subcontrol-origin: margin;\n"
"}\n"
"\n"
"QScrollBar::sub-line:vertical {\n"
"  margin: 3px 0px 3px 0px;\n"
"  border-image: url(\":/qss_icons/rc/arrow_up_disabled.png\");\n"
"  height: 12px;\n"
"  width: 12px;\n"
"  subcontrol-position: top;\n"
"  subcontrol-origin: margin;\n"
"}\n"
"\n"
"QScrollBar::sub-line:vertical:hover, QScrollBar::sub-line:vertical:on {\n"
"  border-image: url(\":/qss_icons/rc/arrow_up.png\");\n"
"  height: 12px;\n"
"  width: 12px;\n"
"  subcontrol-position: top;\n"
"  subcontrol-origin: margin;\n"
"}\n"
"\n"
"QScrollBar::up-arrow:horizontal, QScrollBar::down-arrow:horizontal {\n"
"  background: none;\n"
"}\n"
"\n"
"QScrollBar::up-arrow:vertical, QScrollBar::down-arrow:vertical {\n"
"  background: none;\n"
"}\n"
"\n"
"QScrollBar::add-page:horizontal, QScrollBar::sub-page:horizontal {\n"
"  background: none;\n"
"}\n"
"\n"
"QScrollBar::add-page:vertical, QScrollBar::sub-page:vertical {\n"
"  background: none;\n"
"}\n"
"\n"
"/* QTextEdit --------------------------------------------------------------\n"
"\n"
"https://doc.qt.io/qt-5/stylesheet-examples.html#customizing-specific-widgets\n"
"\n"
"--------------------------------------------------------------------------- */\n"
"QTextEdit {\n"
"  background-color: #19232D;\n"
"  color: #F0F0F0;\n"
"  border: 1px solid #32414B;\n"
"}\n"
"\n"
"QTextEdit:hover {\n"
"  border: 1px solid #148CD2;\n"
"  color: #F0F0F0;\n"
"}\n"
"\n"
"QTextEdit:selected {\n"
"  background: #1464A0;\n"
"  color: #32414B;\n"
"}\n"
"\n"
"/* QPlainTextEdit ---------------------------------------------------------\n"
"\n"
"--------------------------------------------------------------------------- */\n"
"QPlainTextEdit {\n"
"  background-color: #19232D;\n"
"  color: #F0F0F0;\n"
"  border-radius: 4px;\n"
"  border: 1px solid #32414B;\n"
"}\n"
"\n"
"QPlainTextEdit:hover {\n"
"  border: 1px solid #148CD2;\n"
"  color: #F0F0F0;\n"
"}\n"
"\n"
"QPlainTextEdit:selected {\n"
"  background: #1464A0;\n"
"  color: #32414B;\n"
"}\n"
"\n"
"/* QSizeGrip --------------------------------------------------------------\n"
"\n"
"https://doc.qt.io/qt-5/stylesheet-examples.html#customizing-qsizegrip\n"
"\n"
"--------------------------------------------------------------------------- */\n"
"QSizeGrip {\n"
"  background: transparent;\n"
"  width: 12px;\n"
"  height: 12px;\n"
"  image: url(\":/qss_icons/rc/window_grip.png\");\n"
"}\n"
"\n"
"/* QStackedWidget ---------------------------------------------------------\n"
"\n"
"--------------------------------------------------------------------------- */\n"
"QStackedWidget {\n"
"  padding: 2px;\n"
"  border: 1px solid #32414B;\n"
"  border: 1px solid #19232D;\n"
"}\n"
"\n"
"/* QToolBar ---------------------------------------------------------------\n"
"\n"
"https://doc.qt.io/qt-5/stylesheet-examples.html#customizing-qtoolbar\n"
"\n"
"--------------------------------------------------------------------------- */\n"
"QToolBar {\n"
"  background-color: #32414B;\n"
"  border-bottom: 1px solid #19232D;\n"
"  padding: 2px;\n"
"  font-weight: bold;\n"
"}\n"
"\n"
"QToolBar QToolButton {\n"
"  background-color: #32414B;\n"
"  border: 1px solid #32414B;\n"
"}\n"
"\n"
"QToolBar QToolButton:hover {\n"
"  border: 1px solid #148CD2;\n"
"}\n"
"\n"
"QToolBar QToolButton:checked {\n"
"  border: 1px solid #19232D;\n"
"  background-color: #19232D;\n"
"}\n"
"\n"
"QToolBar QToolButton:checked:hover {\n"
"  border: 1px solid #148CD2;\n"
"}\n"
"\n"
"QToolBar::handle:horizontal {\n"
"  width: 16px;\n"
"  image: url(\":/qss_icons/rc/toolbar_move_horizontal.png\");\n"
"}\n"
"\n"
"QToolBar::handle:vertical {\n"
"  height: 16px;\n"
"  image: url(\":/qss_icons/rc/toolbar_move_horizontal.png\");\n"
"}\n"
"\n"
"QToolBar::separator:horizontal {\n"
"  width: 16px;\n"
"  image: url(\":/qss_icons/rc/toolbar_separator_horizontal.png\");\n"
"}\n"
"\n"
"QToolBar::separator:vertical {\n"
"  height: 16px;\n"
"  image: url(\":/qss_icons/rc/toolbar_separator_vertical.png\");\n"
"}\n"
"\n"
"QToolButton#qt_toolbar_ext_button {\n"
"  background: #32414B;\n"
"  border: 0px;\n"
"  color: #F0F0F0;\n"
"  image: url(\":/qss_icons/rc/arrow_right.png\");\n"
"}\n"
"\n"
"/* QAbstractSpinBox -------------------------------------------------------\n"
"\n"
"--------------------------------------------------------------------------- */\n"
"QAbstractSpinBox {\n"
"  background-color: #19232D;\n"
"  border: 1px solid #32414B;\n"
"  color: #F0F0F0;\n"
"  /* This fixes 103, 111 */\n"
"  padding-top: 2px;\n"
"  /* This fixes 103, 111 */\n"
"  padding-bottom: 2px;\n"
"  padding-left: 4px;\n"
"  padding-right: 4px;\n"
"  border-radius: 4px;\n"
"  /* min-width: 5px; removed to fix 109 */\n"
"}\n"
"\n"
"QAbstractSpinBox:up-button {\n"
"  background-color: transparent #19232D;\n"
"  subcontrol-origin: border;\n"
"  subcontrol-position: top right;\n"
"  border-left: 1px solid #32414B;\n"
"  margin: 1px;\n"
"}\n"
"\n"
"QAbstractSpinBox::up-arrow, QAbstractSpinBox::up-arrow:disabled, QAbstractSpinBox::up-arrow:off {\n"
"  image: url(\":/qss_icons/rc/arrow_up_disabled.png\");\n"
"  height: 12px;\n"
"  width: 12px;\n"
"}\n"
"\n"
"QAbstractSpinBox::up-arrow:hover {\n"
"  image: url(\":/qss_icons/rc/arrow_up.png\");\n"
"}\n"
"\n"
"QAbstractSpinBox:down-button {\n"
"  background-color: transparent #19232D;\n"
"  subcontrol-origin: border;\n"
"  subcontrol-position: bottom right;\n"
"  border-left: 1px solid #32414B;\n"
"  margin: 1px;\n"
"}\n"
"\n"
"QAbstractSpinBox::down-arrow, QAbstractSpinBox::down-arrow:disabled, QAbstractSpinBox::down-arrow:off {\n"
"  image: url(\":/qss_icons/rc/arrow_down_disabled.png\");\n"
"  height: 12px;\n"
"  width: 12px;\n"
"}\n"
"\n"
"QAbstractSpinBox::down-arrow:hover {\n"
"  image: url(\":/qss_icons/rc/arrow_down.png\");\n"
"}\n"
"\n"
"QAbstractSpinBox:hover {\n"
"  border: 1px solid #148CD2;\n"
"  color: #F0F0F0;\n"
"}\n"
"\n"
"QAbstractSpinBox:selected {\n"
"  background: #1464A0;\n"
"  color: #32414B;\n"
"}\n"
"\n"
"/* ------------------------------------------------------------------------ */\n"
"/* DISPLAYS --------------------------------------------------------------- */\n"
"/* ------------------------------------------------------------------------ */\n"
"/* QLabel -----------------------------------------------------------------\n"
"\n"
"https://doc.qt.io/qt-5/stylesheet-examples.html#customizing-qframe\n"
"\n"
"--------------------------------------------------------------------------- */\n"
"QLabel {\n"
"  background-color: #19232D;\n"
"  border: 0px solid #32414B;\n"
"  padding: 2px;\n"
"  margin: 0px;\n"
"  color: #F0F0F0;\n"
"}\n"
"\n"
"QLabel::disabled {\n"
"  background-color: #19232D;\n"
"  border: 0px solid #32414B;\n"
"  color: #787878;\n"
"}\n"
"\n"
"/* QTextBrowser -----------------------------------------------------------\n"
"\n"
"https://doc.qt.io/qt-5/stylesheet-examples.html#customizing-qabstractscrollarea\n"
"\n"
"--------------------------------------------------------------------------- */\n"
"QTextBrowser {\n"
"  background-color: #19232D;\n"
"  border: 1px solid #32414B;\n"
"  color: #F0F0F0;\n"
"  border-radius: 4px;\n"
"}\n"
"\n"
"QTextBrowser:disabled {\n"
"  background-color: #19232D;\n"
"  border: 1px solid #32414B;\n"
"  color: #787878;\n"
"  border-radius: 4px;\n"
"}\n"
"\n"
"QTextBrowser:hover, QTextBrowser:!hover, QTextBrowser::selected, QTextBrowser::pressed {\n"
"  border: 1px solid #32414B;\n"
"}\n"
"\n"
"/* QGraphicsView ----------------------------------------------------------\n"
"\n"
"--------------------------------------------------------------------------- */\n"
"QGraphicsView {\n"
"  background-color: #19232D;\n"
"  border: 1px solid #32414B;\n"
"  color: #F0F0F0;\n"
"  border-radius: 4px;\n"
"}\n"
"\n"
"QGraphicsView:disabled {\n"
"  background-color: #19232D;\n"
"  border: 1px solid #32414B;\n"
"  color: #787878;\n"
"  border-radius: 4px;\n"
"}\n"
"\n"
"QGraphicsView:hover, QGraphicsView:!hover, QGraphicsView::selected, QGraphicsView::pressed {\n"
"  border: 1px solid #32414B;\n"
"}\n"
"\n"
"/* QCalendarWidget --------------------------------------------------------\n"
"\n"
"--------------------------------------------------------------------------- */\n"
"QCalendarWidget {\n"
"  border: 1px solid #32414B;\n"
"  border-radius: 4px;\n"
"}\n"
"\n"
"QCalendarWidget:disabled {\n"
"  background-color: #19232D;\n"
"  color: #787878;\n"
"}\n"
"\n"
"/* QLCDNumber -------------------------------------------------------------\n"
"\n"
"--------------------------------------------------------------------------- */\n"
"QLCDNumber {\n"
"  background-color: #19232D;\n"
"  color: #F0F0F0;\n"
"}\n"
"\n"
"QLCDNumber:disabled {\n"
"  background-color: #19232D;\n"
"  color: #787878;\n"
"}\n"
"\n"
"/* QProgressBar -----------------------------------------------------------\n"
"\n"
"https://doc.qt.io/qt-5/stylesheet-examples.html#customizing-qprogressbar\n"
"\n"
"--------------------------------------------------------------------------- */\n"
"QProgressBar {\n"
"  background-color: #19232D;\n"
"  border: 1px solid #32414B;\n"
"  color: #F0F0F0;\n"
"  border-radius: 4px;\n"
"  text-align: center;\n"
"}\n"
"\n"
"QProgressBar:disabled {\n"
"  background-color: #19232D;\n"
"  border: 1px solid #32414B;\n"
"  color: #787878;\n"
"  border-radius: 4px;\n"
"  text-align: center;\n"
"}\n"
"\n"
"QProgressBar::chunk {\n"
"  background-color: #1464A0;\n"
"  color: #19232D;\n"
"  border-radius: 4px;\n"
"}\n"
"\n"
"QProgressBar::chunk:disabled {\n"
"  background-color: #14506E;\n"
"  color: #787878;\n"
"  border-radius: 4px;\n"
"}\n"
"\n"
"/* ------------------------------------------------------------------------ */\n"
"/* BUTTONS ---------------------------------------------------------------- */\n"
"/* ------------------------------------------------------------------------ */\n"
"/* QPushButton ------------------------------------------------------------\n"
"\n"
"https://doc.qt.io/qt-5/stylesheet-examples.html#customizing-qpushbutton\n"
"\n"
"--------------------------------------------------------------------------- */\n"
"QPushButton {\n"
"  background-color: #505F69;\n"
"  border: 1px solid #32414B;\n"
"  color: #F0F0F0;\n"
"  border-radius: 4px;\n"
"  padding: 3px;\n"
"  outline: none;\n"
"}\n"
"\n"
"QPushButton:disabled {\n"
"  background-color: #32414B;\n"
"  border: 1px solid #32414B;\n"
"  color: #787878;\n"
"  border-radius: 4px;\n"
"  padding: 3px;\n"
"}\n"
"\n"
"QPushButton:checked {\n"
"  background-color: #32414B;\n"
"  border: 1px solid #32414B;\n"
"  border-radius: 4px;\n"
"  padding: 3px;\n"
"  outline: none;\n"
"}\n"
"\n"
"QPushButton:checked:disabled {\n"
"  background-color: #19232D;\n"
"  border: 1px solid #32414B;\n"
"  color: #787878;\n"
"  border-radius: 4px;\n"
"  padding: 3px;\n"
"  outline: none;\n"
"}\n"
"\n"
"QPushButton:checked:selected {\n"
"  background: #1464A0;\n"
"  color: #32414B;\n"
"}\n"
"\n"
"QPushButton:checked:hover {\n"
"  border: 1px solid #148CD2;\n"
"  color: #F0F0F0;\n"
"}\n"
"\n"
"QPushButton::menu-indicator {\n"
"  subcontrol-origin: padding;\n"
"  subcontrol-position: bottom right;\n"
"  bottom: 4px;\n"
"}\n"
"\n"
"QPushButton:pressed {\n"
"  background-color: #19232D;\n"
"  border: 1px solid #19232D;\n"
"}\n"
"\n"
"QPushButton:pressed:hover {\n"
"  border: 1px solid #148CD2;\n"
"}\n"
"\n"
"QPushButton:hover {\n"
"  border: 1px solid #148CD2;\n"
"  color: #F0F0F0;\n"
"}\n"
"\n"
"QPushButton:selected {\n"
"  background: #1464A0;\n"
"  color: #32414B;\n"
"}\n"
"\n"
"/* QToolButton ------------------------------------------------------------\n"
"\n"
"https://doc.qt.io/qt-5/stylesheet-examples.html#customizing-qtoolbutton\n"
"\n"
"--------------------------------------------------------------------------- */\n"
"QToolButton {\n"
"  background-color: transparent;\n"
"  border-radius: 4px;\n"
"  margin: 0px;\n"
"  padding: 2px;\n"
"  /* The subcontrols below are used only in the MenuButtonPopup mode */\n"
"  /* The subcontrol below is used only in the InstantPopup or DelayedPopup mode */\n"
"}\n"
"\n"
"QToolButton:checked {\n"
"  background-color: transparent;\n"
"  border: 1px solid #1464A0;\n"
"}\n"
"\n"
"QToolButton:checked:disabled {\n"
"  border: 1px solid #14506E;\n"
"}\n"
"\n"
"QToolButton:pressed {\n"
"  margin: 1px;\n"
"  background-color: transparent;\n"
"  border: 1px solid #1464A0;\n"
"}\n"
"\n"
"QToolButton:disabled {\n"
"  border: none;\n"
"}\n"
"\n"
"QToolButton:disabled:hover {\n"
"  border: 1px solid #32414B;\n"
"}\n"
"\n"
"QToolButton:hover {\n"
"  border: 1px solid #148CD2;\n"
"}\n"
"\n"
"QToolButton[popupMode=\"1\"] {\n"
"  padding: 2px;\n"
"  /* Only for MenuButtonPopup */\n"
"  padding-right: 12px;\n"
"  /* Make way for the popup button */\n"
"  border: 1px solid #32414B;\n"
"  border-radius: 4px;\n"
"}\n"
"\n"
"QToolButton[popupMode=\"2\"] {\n"
"  padding: 2px;\n"
"  /* Only for InstantPopup */\n"
"  padding-right: 12px;\n"
"  /* Make way for the popup button */\n"
"  border: 1px solid #32414B;\n"
"}\n"
"\n"
"QToolButton::menu-button {\n"
"  padding: 2px;\n"
"  border-radius: 4px;\n"
"  border: 1px solid #32414B;\n"
"  border-top-right-radius: 4px;\n"
"  border-bottom-right-radius: 4px;\n"
"  /* 16px width + 4px for border = 20px allocated above */\n"
"  width: 16px;\n"
"  outline: none;\n"
"}\n"
"\n"
"QToolButton::menu-button:hover {\n"
"  border: 1px solid #148CD2;\n"
"}\n"
"\n"
"QToolButton::menu-button:checked:hover {\n"
"  border: 1px solid #148CD2;\n"
"}\n"
"\n"
"QToolButton::menu-indicator {\n"
"  image: url(\":/qss_icons/rc/arrow_down.png\");\n"
"  height: 12px;\n"
"  width: 12px;\n"
"  top: -8px;\n"
"  /* Shift it a bit */\n"
"  left: -4px;\n"
"  /* Shift it a bit */\n"
"}\n"
"\n"
"QToolButton::menu-arrow {\n"
"  image: url(\":/qss_icons/rc/arrow_down.png\");\n"
"  height: 12px;\n"
"  width: 12px;\n"
"}\n"
"\n"
"QToolButton::menu-arrow:open {\n"
"  border: 1px solid #32414B;\n"
"}\n"
"\n"
"/* QCommandLinkButton -----------------------------------------------------\n"
"\n"
"--------------------------------------------------------------------------- */\n"
"QCommandLinkButton {\n"
"  background-color: transparent;\n"
"  border: 1px solid #32414B;\n"
"  color: #F0F0F0;\n"
"  border-radius: 4px;\n"
"  padding: 0px;\n"
"  margin: 0px;\n"
"}\n"
"\n"
"QCommandLinkButton:disabled {\n"
"  background-color: transparent;\n"
"  color: #787878;\n"
"}\n"
"\n"
"/* ------------------------------------------------------------------------ */\n"
"/* INPUTS - NO FIELDS ----------------------------------------------------- */\n"
"/* ------------------------------------------------------------------------ */\n"
"/* QComboBox --------------------------------------------------------------\n"
"\n"
"https://doc.qt.io/qt-5/stylesheet-examples.html#customizing-qcombobox\n"
"\n"
"--------------------------------------------------------------------------- */\n"
"QComboBox {\n"
"  border: 1px solid #32414B;\n"
"  border-radius: 4px;\n"
"  selection-background-color: #1464A0;\n"
"  padding-left: 4px;\n"
"  padding-right: 4px;\n"
"  /* Fixes #103, #111 */\n"
"  min-height: 1.5em;\n"
"  /* padding-top: 2px;     removed to fix #132 */\n"
"  /* padding-bottom: 2px;  removed to fix #132 */\n"
"  /* min-width: 75px;      removed to fix #109 */\n"
"  /* Needed to remove indicator - fix #132 */\n"
"}\n"
"\n"
"QComboBox QAbstractItemView {\n"
"  background-color: #19232D;\n"
"  border-radius: 4px;\n"
"  border: 1px solid #32414B;\n"
"  selection-color: #148CD2;\n"
"  selection-background-color: #32414B;\n"
"}\n"
"\n"
"QComboBox:disabled {\n"
"  background-color: #19232D;\n"
"  color: #787878;\n"
"}\n"
"\n"
"QComboBox:hover {\n"
"  border: 1px solid #148CD2;\n"
"}\n"
"\n"
"QComboBox:on {\n"
"  selection-background-color: #19232D;\n"
"}\n"
"\n"
"QComboBox::indicator {\n"
"  background-color: transparent;\n"
"  selection-background-color: transparent;\n"
"  color: transparent;\n"
"  selection-color: transparent;\n"
"  /* Needed to remove indicator - fix #132 */\n"
"}\n"
"\n"
"QComboBox::indicator:alternate {\n"
"  background: #19232D;\n"
"}\n"
"\n"
"QComboBox::item:alternate {\n"
"  background: #19232D;\n"
"}\n"
"\n"
"QComboBox::item:checked {\n"
"  font-weight: bold;\n"
"}\n"
"\n"
"QComboBox::item:selected {\n"
"  border: 0px solid transparent;\n"
"}\n"
"\n"
"QComboBox::drop-down {\n"
"  subcontrol-origin: padding;\n"
"  subcontrol-position: top right;\n"
"  width: 20px;\n"
"  border-left-width: 0px;\n"
"  border-left-color: #32414B;\n"
"  border-left-style: solid;\n"
"  border-top-right-radius: 3px;\n"
"  border-bottom-right-radius: 3px;\n"
"}\n"
"\n"
"QComboBox::down-arrow {\n"
"  image: url(\":/qss_icons/rc/arrow_down_disabled.png\");\n"
"  height: 12px;\n"
"  width: 12px;\n"
"}\n"
"\n"
"QComboBox::down-arrow:on, QComboBox::down-arrow:hover, QComboBox::down-arrow:focus {\n"
"  image: url(\":/qss_icons/rc/arrow_down.png\");\n"
"}\n"
"\n"
"/* QSlider ----------------------------------------------------------------\n"
"\n"
"https://doc.qt.io/qt-5/stylesheet-examples.html#customizing-qslider\n"
"\n"
"--------------------------------------------------------------------------- */\n"
"QSlider:disabled {\n"
"  background: #19232D;\n"
"}\n"
"\n"
"QSlider:focus {\n"
"  border: none;\n"
"}\n"
"\n"
"QSlider::groove:horizontal {\n"
"  background: #32414B;\n"
"  border: 1px solid #32414B;\n"
"  height: 4px;\n"
"  margin: 0px;\n"
"  border-radius: 4px;\n"
"}\n"
"\n"
"QSlider::groove:vertical {\n"
"  background: #32414B;\n"
"  border: 1px solid #32414B;\n"
"  width: 4px;\n"
"  margin: 0px;\n"
"  border-radius: 4px;\n"
"}\n"
"\n"
"QSlider::add-page:vertical {\n"
"  background: #1464A0;\n"
"  border: 1px solid #32414B;\n"
"  width: 4px;\n"
"  margin: 0px;\n"
"  border-radius: 4px;\n"
"}\n"
"\n"
"QSlider::add-page:vertical :disabled {\n"
"  background: #14506E;\n"
"}\n"
"\n"
"QSlider::sub-page:horizontal {\n"
"  background: #1464A0;\n"
"  border: 1px solid #32414B;\n"
"  height: 4px;\n"
"  margin: 0px;\n"
"  border-radius: 4px;\n"
"}\n"
"\n"
"QSlider::sub-page:horizontal:disabled {\n"
"  background: #14506E;\n"
"}\n"
"\n"
"QSlider::handle:horizontal {\n"
"  background: #787878;\n"
"  border: 1px solid #32414B;\n"
"  width: 8px;\n"
"  height: 8px;\n"
"  margin: -8px 0px;\n"
"  border-radius: 4px;\n"
"}\n"
"\n"
"QSlider::handle:horizontal:hover {\n"
"  background: #148CD2;\n"
"  border: 1px solid #148CD2;\n"
"}\n"
"\n"
"QSlider::handle:vertical {\n"
"  background: #787878;\n"
"  border: 1px solid #32414B;\n"
"  width: 8px;\n"
"  height: 8px;\n"
"  margin: 0 -8px;\n"
"  border-radius: 4px;\n"
"}\n"
"\n"
"QSlider::handle:vertical:hover {\n"
"  background: #148CD2;\n"
"  border: 1px solid #148CD2;\n"
"}\n"
"\n"
"/* QLineEdit --------------------------------------------------------------\n"
"\n"
"https://doc.qt.io/qt-5/stylesheet-examples.html#customizing-qlineedit\n"
"\n"
"--------------------------------------------------------------------------- */\n"
"QLineEdit {\n"
"  background-color: #19232D;\n"
"  padding-top: 2px;\n"
"  /* This QLineEdit fix  103, 111 */\n"
"  padding-bottom: 2px;\n"
"  /* This QLineEdit fix  103, 111 */\n"
"  padding-left: 4px;\n"
"  padding-right: 4px;\n"
"  border-style: solid;\n"
"  border: 1px solid #32414B;\n"
"  border-radius: 4px;\n"
"  color: #F0F0F0;\n"
"}\n"
"\n"
"QLineEdit:disabled {\n"
"  background-color: #19232D;\n"
"  color: #787878;\n"
"}\n"
"\n"
"QLineEdit:hover {\n"
"  border: 1px solid #148CD2;\n"
"  color: #F0F0F0;\n"
"}\n"
"\n"
"QLineEdit:selected {\n"
"  background: #1464A0;\n"
"  color: #32414B;\n"
"}\n"
"\n"
"/* QTabWiget ---------")
        self.centralwidget = QtWidgets.QWidget(MainWindow)
        self.centralwidget.setObjectName("centralwidget")
        self.formLayout = QtWidgets.QFormLayout(self.centralwidget)
        self.formLayout.setObjectName("formLayout")
        self.gridLayout = QtWidgets.QGridLayout()
        self.gridLayout.setObjectName("gridLayout")
        self.tabWidget = QtWidgets.QTabWidget(self.centralwidget)
        font = QtGui.QFont()
        font.setFamily("Gabriola")
        font.setPointSize(11)
        self.tabWidget.setFont(font)
        self.tabWidget.setCursor(QtGui.QCursor(QtCore.Qt.ArrowCursor))
        self.tabWidget.setStyleSheet("QTabWidget::pane { /* The tab widget frame */\n"
"border-top: 2px solid #0E2F44;\n"
"}\n"
"QTabWidget::tab-bar {\n"
"left: 5px; /* move to the right by 5px */\n"
"}\n"
"/* Style the tab using the tab sub-control. Note that it reads QTabBar _not_ QTabWidget */\n"
"QTabBar::tab {\n"
"background-color : #0E2F44;\n"
"border: 2px solid #0E2F44;\n"
"border-bottom-color: #0E2F44; /* same as the pane color */\n"
"border-top-left-radius: 4px;\n"
"border-top-right-radius: 4px;\n"
"min-width: 8ex;\n"
"padding: 2px;\n"
"}\n"
"QTabBar::tab:selected, QTabBar::tab:hover {\n"
"background:#0E2F44\n"
"}\n"
"QTabBar::tab:selected {\n"
"border-color: #0E2F44;\n"
"border-bottom-color: #0E2F44; /* same as pane color */\n"
"}\n"
"QTabBar::tab:!selected {\n"
"margin-top: 2px; /* make non-selected tabs look smaller */\n"
"}")
        self.tabWidget.setMovable(True)
        self.tabWidget.setObjectName("tabWidget")
        self.tab = QtWidgets.QWidget()
        self.tab.setObjectName("tab")
        self.gridLayout_4 = QtWidgets.QGridLayout(self.tab)
        self.gridLayout_4.setObjectName("gridLayout_4")
        self.label_6 = QtWidgets.QLabel(self.tab)
        font = QtGui.QFont()
        font.setFamily("Modern")
        font.setPointSize(11)
        self.label_6.setFont(font)
        self.label_6.setObjectName("label_6")
        self.gridLayout_4.addWidget(self.label_6, 11, 0, 1, 1)
        self.label_4 = QtWidgets.QLabel(self.tab)
        font = QtGui.QFont()
        font.setFamily("Modern")
        font.setPointSize(11)
        self.label_4.setFont(font)
        self.label_4.setObjectName("label_4")
        self.gridLayout_4.addWidget(self.label_4, 7, 0, 1, 1)
        self.horizontalLayout = QtWidgets.QHBoxLayout()
        self.horizontalLayout.setObjectName("horizontalLayout")
        self.gridLayout_4.addLayout(self.horizontalLayout, 0, 0, 1, 1)
        self.label_8 = QtWidgets.QLabel(self.tab)
        font = QtGui.QFont()
        font.setFamily("Modern")
        font.setPointSize(11)
        self.label_8.setFont(font)
        self.label_8.setObjectName("label_8")
        self.gridLayout_4.addWidget(self.label_8, 3, 1, 1, 1)
        self.label_9 = QtWidgets.QLabel(self.tab)
        font = QtGui.QFont()
        font.setFamily("Modern")
        font.setPointSize(11)
        self.label_9.setFont(font)
        self.label_9.setObjectName("label_9")
        self.gridLayout_4.addWidget(self.label_9, 5, 1, 1, 1)
        self.plainTextEdit_6 = QtWidgets.QPlainTextEdit(self.tab)
        font = QtGui.QFont()
        font.setFamily("Gabriola")
        font.setPointSize(16)
        self.plainTextEdit_6.setFont(font)
        self.plainTextEdit_6.setObjectName("plainTextEdit_6")
        self.gridLayout_4.addWidget(self.plainTextEdit_6, 12, 0, 1, 1)
        self.plainTextEdit_2 = QtWidgets.QPlainTextEdit(self.tab)
        font = QtGui.QFont()
        font.setFamily("Segoe UI")
        font.setPointSize(16)
        self.plainTextEdit_2.setFont(font)
        self.plainTextEdit_2.setObjectName("plainTextEdit_2")
        self.gridLayout_4.addWidget(self.plainTextEdit_2, 4, 0, 1, 1)
        self.plainTextEdit_3 = QtWidgets.QPlainTextEdit(self.tab)
        font = QtGui.QFont()
        font.setFamily("Gabriola")
        font.setPointSize(16)
        self.plainTextEdit_3.setFont(font)
        self.plainTextEdit_3.setObjectName("plainTextEdit_3")
        self.gridLayout_4.addWidget(self.plainTextEdit_3, 6, 0, 1, 1)
        self.label_5 = QtWidgets.QLabel(self.tab)
        font = QtGui.QFont()
        font.setFamily("Modern")
        font.setPointSize(11)
        self.label_5.setFont(font)
        self.label_5.setObjectName("label_5")
        self.gridLayout_4.addWidget(self.label_5, 9, 0, 1, 1)
        self.label_10 = QtWidgets.QLabel(self.tab)
        font = QtGui.QFont()
        font.setFamily("Modern")
        font.setPointSize(11)
        self.label_10.setFont(font)
        self.label_10.setObjectName("label_10")
        self.gridLayout_4.addWidget(self.label_10, 7, 1, 1, 1)
        self.label_2 = QtWidgets.QLabel(self.tab)
        font = QtGui.QFont()
        font.setFamily("Modern")
        font.setPointSize(11)
        self.label_2.setFont(font)
        self.label_2.setObjectName("label_2")
        self.gridLayout_4.addWidget(self.label_2, 3, 0, 1, 1)
        self.label = QtWidgets.QLabel(self.tab)
        font = QtGui.QFont()
        font.setFamily("Modern")
        font.setPointSize(11)
        self.label.setFont(font)
        self.label.setObjectName("label")
        self.gridLayout_4.addWidget(self.label, 1, 0, 1, 1)
        self.label_3 = QtWidgets.QLabel(self.tab)
        font = QtGui.QFont()
        font.setFamily("Modern")
        font.setPointSize(11)
        self.label_3.setFont(font)
        self.label_3.setObjectName("label_3")
        self.gridLayout_4.addWidget(self.label_3, 5, 0, 1, 1)
        self.plainTextEdit_9 = QtWidgets.QPlainTextEdit(self.tab)
        font = QtGui.QFont()
        font.setFamily("Gabriola")
        font.setPointSize(16)
        self.plainTextEdit_9.setFont(font)
        self.plainTextEdit_9.setObjectName("plainTextEdit_9")
        self.gridLayout_4.addWidget(self.plainTextEdit_9, 6, 1, 1, 1)
        self.plainTextEdit_7 = QtWidgets.QPlainTextEdit(self.tab)
        font = QtGui.QFont()
        font.setFamily("Gabriola")
        font.setPointSize(16)
        self.plainTextEdit_7.setFont(font)
        self.plainTextEdit_7.setObjectName("plainTextEdit_7")
        self.gridLayout_4.addWidget(self.plainTextEdit_7, 2, 1, 1, 1)
        self.plainTextEdit_4 = QtWidgets.QPlainTextEdit(self.tab)
        font = QtGui.QFont()
        font.setFamily("Gabriola")
        font.setPointSize(16)
        self.plainTextEdit_4.setFont(font)
        self.plainTextEdit_4.setObjectName("plainTextEdit_4")
        self.gridLayout_4.addWidget(self.plainTextEdit_4, 8, 0, 1, 1)
        self.plainTextEdit_10 = QtWidgets.QPlainTextEdit(self.tab)
        font = QtGui.QFont()
        font.setFamily("Gabriola")
        font.setPointSize(16)
        self.plainTextEdit_10.setFont(font)
        self.plainTextEdit_10.setObjectName("plainTextEdit_10")
        self.gridLayout_4.addWidget(self.plainTextEdit_10, 8, 1, 1, 1)
        self.plainTextEdit = QtWidgets.QPlainTextEdit(self.tab)
        font = QtGui.QFont()
        font.setFamily("Segoe Print")
        font.setPointSize(16)
        self.plainTextEdit.setFont(font)
        self.plainTextEdit.setObjectName("plainTextEdit")
        self.gridLayout_4.addWidget(self.plainTextEdit, 2, 0, 1, 1)
        self.plainTextEdit_5 = QtWidgets.QPlainTextEdit(self.tab)
        font = QtGui.QFont()
        font.setFamily("Gabriola")
        font.setPointSize(16)
        self.plainTextEdit_5.setFont(font)
        self.plainTextEdit_5.setObjectName("plainTextEdit_5")
        self.gridLayout_4.addWidget(self.plainTextEdit_5, 10, 0, 1, 1)
        self.label_7 = QtWidgets.QLabel(self.tab)
        font = QtGui.QFont()
        font.setFamily("Modern")
        font.setPointSize(11)
        self.label_7.setFont(font)
        self.label_7.setObjectName("label_7")
        self.gridLayout_4.addWidget(self.label_7, 1, 1, 1, 1)
        self.plainTextEdit_8 = QtWidgets.QPlainTextEdit(self.tab)
        font = QtGui.QFont()
        font.setFamily("Gabriola")
        font.setPointSize(16)
        self.plainTextEdit_8.setFont(font)
        self.plainTextEdit_8.setObjectName("plainTextEdit_8")
        self.gridLayout_4.addWidget(self.plainTextEdit_8, 4, 1, 1, 1)
        self.pushButton = QtWidgets.QPushButton(self.tab)
        font = QtGui.QFont()
        font.setFamily("Modern")
        font.setPointSize(22)
        font.setBold(True)
        font.setItalic(True)
        font.setUnderline(True)
        font.setWeight(75)
        self.pushButton.setFont(font)
        self.pushButton.setObjectName("pushButton")
        self.gridLayout_4.addWidget(self.pushButton, 10, 1, 1, 1)
        self.comboBox_4 = QtWidgets.QComboBox(self.tab)
        self.comboBox_4.setObjectName("comboBox_4")
        self.comboBox_4.addItem("")
        self.comboBox_4.addItem("")
        self.gridLayout_4.addWidget(self.comboBox_4, 12, 1, 1, 1)
        self.tabWidget.addTab(self.tab, "")
        self.tab_3 = QtWidgets.QWidget()
        self.tab_3.setObjectName("tab_3")
        self.verticalLayout = QtWidgets.QVBoxLayout(self.tab_3)
        self.verticalLayout.setObjectName("verticalLayout")
        self.label_11 = QtWidgets.QLabel(self.tab_3)
        font = QtGui.QFont()
        font.setFamily("Modern")
        font.setPointSize(11)
        self.label_11.setFont(font)
        self.label_11.setObjectName("label_11")
        self.verticalLayout.addWidget(self.label_11)
        self.label_12 = QtWidgets.QLabel(self.tab_3)
        font = QtGui.QFont()
        font.setFamily("Modern")
        font.setPointSize(11)
        self.label_12.setFont(font)
        self.label_12.setObjectName("label_12")
        self.verticalLayout.addWidget(self.label_12)
        self.comboBox = QtWidgets.QComboBox(self.tab_3)
        font = QtGui.QFont()
        font.setFamily("Segoe Print")
        font.setPointSize(12)
        self.comboBox.setFont(font)
        self.comboBox.setObjectName("comboBox")
        self.verticalLayout.addWidget(self.comboBox)
        self.label_13 = QtWidgets.QLabel(self.tab_3)
        font = QtGui.QFont()
        font.setFamily("Modern")
        font.setPointSize(11)
        self.label_13.setFont(font)
        self.label_13.setObjectName("label_13")
        self.verticalLayout.addWidget(self.label_13)
        self.comboBox_2 = QtWidgets.QComboBox(self.tab_3)
        font = QtGui.QFont()
        font.setFamily("Segoe Print")
        font.setPointSize(12)
        self.comboBox_2.setFont(font)
        self.comboBox_2.setObjectName("comboBox_2")
        self.verticalLayout.addWidget(self.comboBox_2)
        self.label_14 = QtWidgets.QLabel(self.tab_3)
        font = QtGui.QFont()
        font.setFamily("Modern")
        font.setPointSize(11)
        self.label_14.setFont(font)
        self.label_14.setObjectName("label_14")
        self.verticalLayout.addWidget(self.label_14)
        self.comboBox_3 = QtWidgets.QComboBox(self.tab_3)
        font = QtGui.QFont()
        font.setFamily("Segoe Print")
        font.setPointSize(12)
        self.comboBox_3.setFont(font)
        self.comboBox_3.setObjectName("comboBox_3")
        self.verticalLayout.addWidget(self.comboBox_3)
        self.pushButton_2 = QtWidgets.QPushButton(self.tab_3)
        font = QtGui.QFont()
        font.setFamily("Modern")
        font.setPointSize(22)
        font.setBold(True)
        font.setWeight(75)
        self.pushButton_2.setFont(font)
        self.pushButton_2.setObjectName("pushButton_2")
        self.verticalLayout.addWidget(self.pushButton_2)
        self.tabWidget.addTab(self.tab_3, "")
        self.tab_2 = QtWidgets.QWidget()
        self.tab_2.setObjectName("tab_2")
        self.gridLayout_5 = QtWidgets.QGridLayout(self.tab_2)
        self.gridLayout_5.setObjectName("gridLayout_5")
        self.textBrowser = QtWidgets.QTextBrowser(self.tab_2)
        font = QtGui.QFont()
        font.setFamily("SimSun")
        font.setPointSize(21)
        self.textBrowser.setFont(font)
        self.textBrowser.setObjectName("textBrowser")
        self.gridLayout_5.addWidget(self.textBrowser, 0, 0, 1, 1)
        self.tabWidget.addTab(self.tab_2, "")
        self.tab_4 = QtWidgets.QWidget()
        self.tab_4.setObjectName("tab_4")
        self.horizontalSlider = QtWidgets.QSlider(self.tab_4)
        self.horizontalSlider.setGeometry(QtCore.QRect(10, 170, 231, 81))
        self.horizontalSlider.setOrientation(QtCore.Qt.Horizontal)
        self.horizontalSlider.setObjectName("horizontalSlider")
        self.verticalSlider = QtWidgets.QSlider(self.tab_4)
        self.verticalSlider.setGeometry(QtCore.QRect(100, 80, 41, 251))
        self.verticalSlider.setOrientation(QtCore.Qt.Vertical)
        self.verticalSlider.setObjectName("verticalSlider")
        self.horizontalSlider_2 = QtWidgets.QSlider(self.tab_4)
        self.horizontalSlider_2.setGeometry(QtCore.QRect(530, 180, 211, 22))
        self.horizontalSlider_2.setOrientation(QtCore.Qt.Horizontal)
        self.horizontalSlider_2.setObjectName("horizontalSlider_2")
        self.verticalSlider_2 = QtWidgets.QSlider(self.tab_4)
        self.verticalSlider_2.setGeometry(QtCore.QRect(620, 100, 51, 201))
        self.verticalSlider_2.setOrientation(QtCore.Qt.Vertical)
        self.verticalSlider_2.setObjectName("verticalSlider_2")
        self.pushButton_3 = QtWidgets.QPushButton(self.tab_4)
        self.pushButton_3.setGeometry(QtCore.QRect(260, 150, 251, 101))
        font = QtGui.QFont()
        font.setFamily("Nirmala UI")
        font.setPointSize(22)
        self.pushButton_3.setFont(font)
        self.pushButton_3.setStyleSheet("background-color: rgb(255, 0, 0);")
        self.pushButton_3.setObjectName("pushButton_3")
        self.tabWidget.addTab(self.tab_4, "")
        self.gridLayout.addWidget(self.tabWidget, 0, 1, 1, 1)
        self.formLayout.setLayout(0, QtWidgets.QFormLayout.SpanningRole, self.gridLayout)
        MainWindow.setCentralWidget(self.centralwidget)
        self.statusbar = QtWidgets.QStatusBar(MainWindow)
        self.statusbar.setObjectName("statusbar")
        MainWindow.setStatusBar(self.statusbar)

        self.retranslateUi(MainWindow)
        self.tabWidget.setCurrentIndex(3)
        QtCore.QMetaObject.connectSlotsByName(MainWindow)

    def retranslateUi(self, MainWindow):
        _translate = QtCore.QCoreApplication.translate
        MainWindow.setWindowTitle(_translate("MainWindow", "MainWindow"))
        self.label_6.setText(_translate("MainWindow", "Motor ESC Pin 1"))
        self.label_4.setText(_translate("MainWindow", "Ulrasonics Pin 1"))
        self.label_8.setText(_translate("MainWindow", "Motor ESC Pin 3"))
        self.label_9.setText(_translate("MainWindow", "Motor ESC Pin 4"))
        self.label_5.setText(_translate("MainWindow", "Ulrasonics Pin 2"))
        self.label_10.setText(_translate("MainWindow", "Gyroscope Pin "))
        self.label_2.setText(_translate("MainWindow", "Transiver Y pin "))
        self.label.setText(_translate("MainWindow", "Transiver X pin "))
        self.label_3.setText(_translate("MainWindow", "Transiver Z pin "))
        self.label_7.setText(_translate("MainWindow", "Motor ESC Pin 2"))
        self.pushButton.setText(_translate("MainWindow", "Apply"))
        self.comboBox_4.setItemText(0, _translate("MainWindow", "ON : Debug"))
        self.comboBox_4.setItemText(1, _translate("MainWindow", "OFF : Debug"))
        self.tabWidget.setTabText(self.tabWidget.indexOf(self.tab), _translate("MainWindow", "Setup Copter"))
        self.label_11.setText(_translate("MainWindow", "Status"))
        self.label_12.setText(_translate("MainWindow", "Conection Type"))
        self.label_13.setText(_translate("MainWindow", "Connection Port"))
        self.label_14.setText(_translate("MainWindow", "Coonection Speed"))
        self.pushButton_2.setText(_translate("MainWindow", "Connect"))
        self.tabWidget.setTabText(self.tabWidget.indexOf(self.tab_3), _translate("MainWindow", "Copter Connection Status"))
        self.tabWidget.setTabText(self.tabWidget.indexOf(self.tab_2), _translate("MainWindow", "Log"))
        self.pushButton_3.setText(_translate("MainWindow", "Unlock control"))
        self.tabWidget.setTabText(self.tabWidget.indexOf(self.tab_4), _translate("MainWindow", "Page"))
