Electrics-Eagles/Electric-Eagles/Tools Code/Died Tools/CopterChecktool/proui.py

# -*- coding: utf-8 -*-

# Form implementation generated from reading ui file 'C:\Users\DroneDeveloper\Documents\CopterChecktool\proui.ui'
#
# Created by: PyQt5 UI code generator 5.13.0
#
# WARNING! All changes made in this file will be lost!


from PyQt5 import QtCore, QtGui, QtWidgets


class Ui_MainWindow(object):
    def setupUi(self, MainWindow):
        MainWindow.setObjectName("MainWindow")
        MainWindow.resize(800, 600)
        self.centralwidget = QtWidgets.QWidget(MainWindow)
        self.centralwidget.setObjectName("centralwidget")
        self.gridLayout = QtWidgets.QGridLayout(self.centralwidget)
        self.gridLayout.setObjectName("gridLayout")
        self.comboBox_2 = QtWidgets.QComboBox(self.centralwidget)
        self.comboBox_2.setObjectName("comboBox_2")
        self.gridLayout.addWidget(self.comboBox_2, 4, 0, 1, 1)
        self.comboBox = QtWidgets.QComboBox(self.centralwidget)
        self.comboBox.setObjectName("comboBox")
        self.gridLayout.addWidget(self.comboBox, 3, 0, 1, 1)
        self.tabWidget = QtWidgets.QTabWidget(self.centralwidget)
        self.tabWidget.setObjectName("tabWidget")
        self.tab = QtWidgets.QWidget()
        self.tab.setObjectName("tab")
        self.gridLayout_14 = QtWidgets.QGridLayout(self.tab)
        self.gridLayout_14.setObjectName("gridLayout_14")
        self.gridLayout_13 = QtWidgets.QGridLayout()
        self.gridLayout_13.setObjectName("gridLayout_13")
        self.graphicsView = QtWidgets.QGraphicsView(self.tab)
        self.graphicsView.setObjectName("graphicsView")
        self.gridLayout_13.addWidget(self.graphicsView, 0, 0, 1, 1)
        self.gridLayout_14.addLayout(self.gridLayout_13, 0, 0, 1, 1)
        self.tabWidget.addTab(self.tab, "")
        self.tab_3 = QtWidgets.QWidget()
        self.tab_3.setObjectName("tab_3")
        self.gridLayout_12 = QtWidgets.QGridLayout(self.tab_3)
        self.gridLayout_12.setObjectName("gridLayout_12")
        self.gridLayout_11 = QtWidgets.QGridLayout()
        self.gridLayout_11.setObjectName("gridLayout_11")
        self.label_9 = QtWidgets.QLabel(self.tab_3)
        self.label_9.setObjectName("label_9")
        self.gridLayout_11.addWidget(self.label_9, 0, 0, 1, 1)
        self.gridLayout_12.addLayout(self.gridLayout_11, 0, 0, 1, 1)
        self.tabWidget.addTab(self.tab_3, "")
        self.tab_2 = QtWidgets.QWidget()
        self.tab_2.setObjectName("tab_2")
        self.gridLayout_3 = QtWidgets.QGridLayout(self.tab_2)
        self.gridLayout_3.setObjectName("gridLayout_3")
        self.label_4 = QtWidgets.QLabel(self.tab_2)
        self.label_4.setObjectName("label_4")
        self.gridLayout_3.addWidget(self.label_4, 0, 3, 1, 1)
        self.label_5 = QtWidgets.QLabel(self.tab_2)
        self.label_5.setObjectName("label_5")
        self.gridLayout_3.addWidget(self.label_5, 0, 5, 1, 1)
        self.label_3 = QtWidgets.QLabel(self.tab_2)
        self.label_3.setObjectName("label_3")
        self.gridLayout_3.addWidget(self.label_3, 0, 2, 1, 1)
        self.label = QtWidgets.QLabel(self.tab_2)
        self.label.setObjectName("label")
        self.gridLayout_3.addWidget(self.label, 0, 0, 1, 1)
        self.gridLayout_8 = QtWidgets.QGridLayout()
        self.gridLayout_8.setObjectName("gridLayout_8")
        self.verticalSlider_4 = QtWidgets.QSlider(self.tab_2)
        self.verticalSlider_4.setOrientation(QtCore.Qt.Vertical)
        self.verticalSlider_4.setObjectName("verticalSlider_4")
        self.gridLayout_8.addWidget(self.verticalSlider_4, 0, 1, 1, 1)
        self.gridLayout_3.addLayout(self.gridLayout_8, 1, 3, 1, 1)
        self.gridLayout_9 = QtWidgets.QGridLayout()
        self.gridLayout_9.setObjectName("gridLayout_9")
        self.label_8 = QtWidgets.QLabel(self.tab_2)
        self.label_8.setText("")
        self.label_8.setObjectName("label_8")
        self.gridLayout_9.addWidget(self.label_8, 0, 0, 1, 1)
        self.gridLayout_3.addLayout(self.gridLayout_9, 1, 4, 1, 1)
        self.gridLayout_7 = QtWidgets.QGridLayout()
        self.gridLayout_7.setObjectName("gridLayout_7")
        self.verticalSlider_3 = QtWidgets.QSlider(self.tab_2)
        self.verticalSlider_3.setOrientation(QtCore.Qt.Vertical)
        self.verticalSlider_3.setObjectName("verticalSlider_3")
        self.gridLayout_7.addWidget(self.verticalSlider_3, 0, 1, 1, 1)
        self.gridLayout_3.addLayout(self.gridLayout_7, 1, 2, 1, 1)
        self.gridLayout_6 = QtWidgets.QGridLayout()
        self.gridLayout_6.setObjectName("gridLayout_6")
        self.verticalSlider_2 = QtWidgets.QSlider(self.tab_2)
        self.verticalSlider_2.setOrientation(QtCore.Qt.Vertical)
        self.verticalSlider_2.setObjectName("verticalSlider_2")
        self.gridLayout_6.addWidget(self.verticalSlider_2, 0, 1, 1, 1)
        self.gridLayout_3.addLayout(self.gridLayout_6, 1, 1, 1, 1)
        self.label_7 = QtWidgets.QLabel(self.tab_2)
        self.label_7.setObjectName("label_7")
        self.gridLayout_3.addWidget(self.label_7, 0, 4, 1, 1)
        self.gridLayout_10 = QtWidgets.QGridLayout()
        self.gridLayout_10.setObjectName("gridLayout_10")
        self.label_6 = QtWidgets.QLabel(self.tab_2)
        self.label_6.setText("")
        self.label_6.setObjectName("label_6")
        self.gridLayout_10.addWidget(self.label_6, 0, 0, 1, 1)
        self.gridLayout_3.addLayout(self.gridLayout_10, 1, 5, 1, 1)
        self.label_2 = QtWidgets.QLabel(self.tab_2)
        self.label_2.setObjectName("label_2")
        self.gridLayout_3.addWidget(self.label_2, 0, 1, 1, 1)
        self.gridLayout_2 = QtWidgets.QGridLayout()
        self.gridLayout_2.setObjectName("gridLayout_2")
        self.verticalSlider = QtWidgets.QSlider(self.tab_2)
        self.verticalSlider.setOrientation(QtCore.Qt.Vertical)
        self.verticalSlider.setObjectName("verticalSlider")
        self.gridLayout_2.addWidget(self.verticalSlider, 0, 1, 1, 1)
        self.gridLayout_3.addLayout(self.gridLayout_2, 1, 0, 1, 1)
        self.tabWidget.addTab(self.tab_2, "")
        self.gridLayout.addWidget(self.tabWidget, 0, 0, 1, 1)
        self.pushButton = QtWidgets.QPushButton(self.centralwidget)
        self.pushButton.setObjectName("pushButton")
        self.gridLayout.addWidget(self.pushButton, 6, 0, 1, 1)
        self.pushButton_2 = QtWidgets.QPushButton(self.centralwidget)
        self.pushButton_2.setObjectName("pushButton_2")
        self.gridLayout.addWidget(self.pushButton_2, 7, 0, 1, 1)
        MainWindow.setCentralWidget(self.centralwidget)
        self.statusbar = QtWidgets.QStatusBar(MainWindow)
        self.statusbar.setObjectName("statusbar")
        MainWindow.setStatusBar(self.statusbar)

        self.retranslateUi(MainWindow)
        self.tabWidget.setCurrentIndex(1)
        QtCore.QMetaObject.connectSlotsByName(MainWindow)

    def retranslateUi(self, MainWindow):
        _translate = QtCore.QCoreApplication.translate
        MainWindow.setWindowTitle(_translate("MainWindow", "MainWindow"))
        self.tabWidget.setTabText(self.tabWidget.indexOf(self.tab), _translate("MainWindow", "Use"))
        self.label_9.setText(_translate("MainWindow", "TextLabel"))
        self.tabWidget.setTabText(self.tabWidget.indexOf(self.tab_3), _translate("MainWindow", "Calibrate"))
        self.label_4.setText(_translate("MainWindow", "Channel 4"))
        self.label_5.setText(_translate("MainWindow", "Ultrasonic status"))
        self.label_3.setText(_translate("MainWindow", "Channel 3"))
        self.label.setText(_translate("MainWindow", "Channel 1 "))
        self.label_7.setText(_translate("MainWindow", "Gyro Check"))
        self.label_2.setText(_translate("MainWindow", "Channel 2"))
        self.tabWidget.setTabText(self.tabWidget.indexOf(self.tab_2), _translate("MainWindow", "Check"))
        self.pushButton.setText(_translate("MainWindow", "Connect"))
        self.pushButton_2.setText(_translate("MainWindow", "Get Data in Loop"))
