Electrics-Eagles/Electric-Eagles/Tools Code/Used Tools/Electrics Eagles IDE SCR/upload_firmware.py

import os

import easygui as easygui
import temp
import serial_api
from zipfile import ZipFile
from serial_api import detect_ports
import subprocess
def upload_firmware_via_cable( path_to_sketch):
    path_to_return = os.path.abspath("")
    os.chdir(os.path.abspath("Arduino"))
    output = subprocess.getoutput("arduino --board arduino:avr:nano:cpu=atmega328old --port " + str(detect_ports()) + " --upload " + path_to_sketch)
    os.chdir(path_to_return)
    return output


pass


def unpack_files_from_zip_and_flash_firmware():
    path_to_zip = easygui.fileopenbox("Open A Zip")
    with ZipFile(path_to_zip, 'r') as zipObj:
        # Extract all the contents of zip file in different directory
        path=temp.tempdir()
        zipObj.extractall(path)
        log=upload_firmware_via_cable(path+ "//Main.ino")
        return log
pass
