Electrics-Eagles/Electric-Eagles/Tools Code/Used Tools/Electrics Eagles IDE SCR/web_api.py

# Run web api
import http.server
import socketserver
import threading
def web_api_run():
    try:


        PORT = 3452
        Handler = http.server.SimpleHTTPRequestHandler

        with socketserver.TCPServer(("localhost", PORT), Handler) as httpd:
            print("serving at port", PORT)
            httpd.serve_forever()
    except Exception as error :
        print(error)

pass
def web_api_thread():
    to=threading.Thread(target=web_api_run)
    to.start()
pass
